prakashlab/octopi-driver-board/Parts/Connectors/FunctionMAX FX20/FX20-120S-0.5SV Specs.pdf

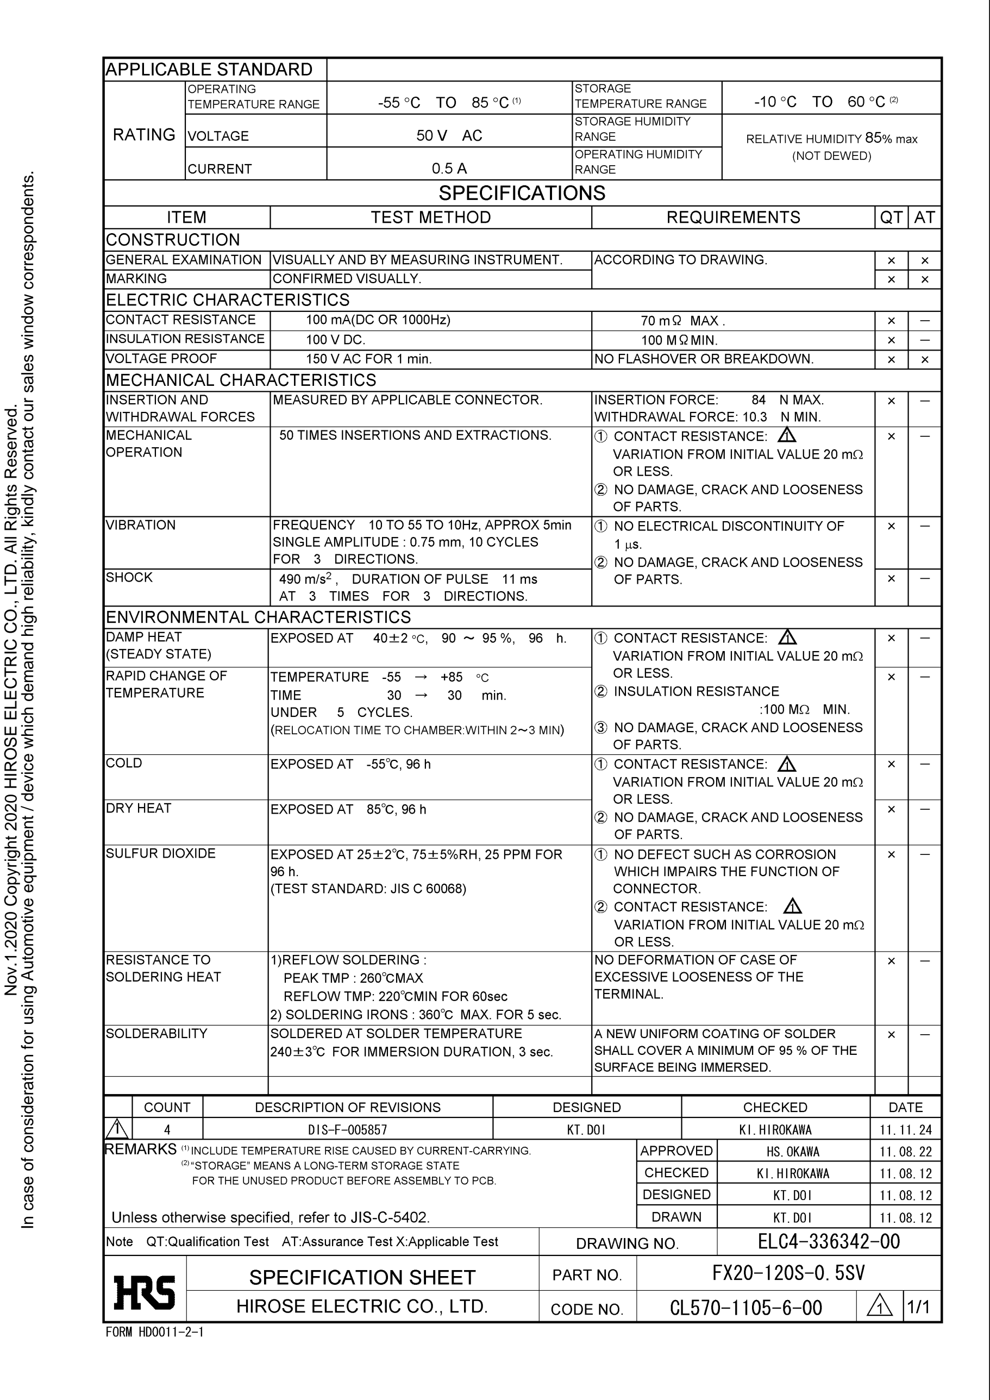
[picture p6: page 1]
