prakashlab/octopi-driver-board/ODSv1.0.0-BP-Jmp/Mechanical Renders/Below Front.png

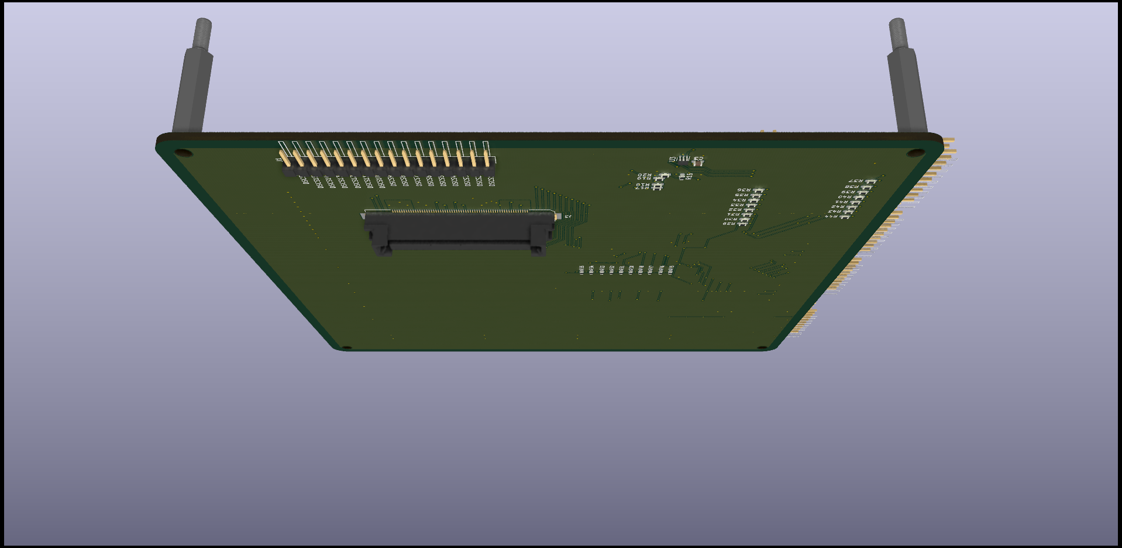
ODSv1.0.0-BP-Jmp/Mechanical Renders/Below Front.png
