prakashlab/octopi-driver-board/ODSv1.0.0-BP-Jmp/Preview Renders/Bottom.png

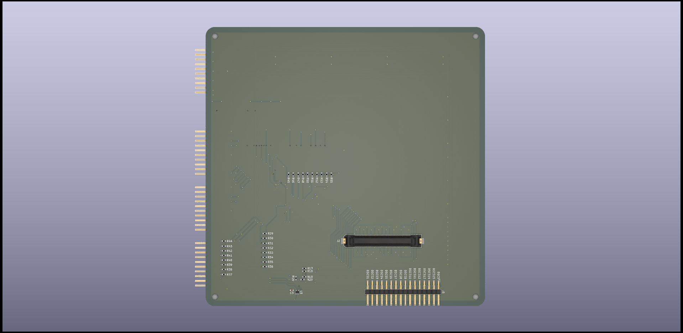
ODSv1.0.0-BP-Jmp/Preview Renders/Bottom.png
