prakashlab/octopi-driver-board/ODSv1.0.0-BP-Jmp/Preview Renders/Top.png

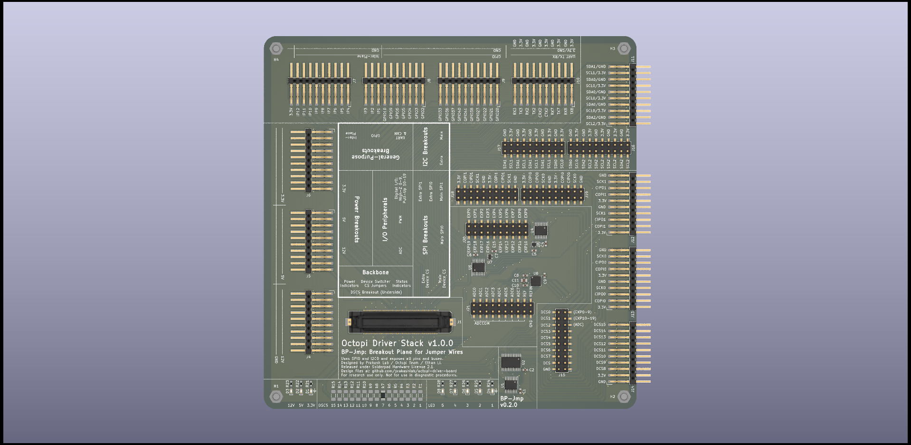
ODSv1.0.0-BP-Jmp/Preview Renders/Top.png
