prakashlab/octopi-driver-board/ODSv1.0.0-BT/Preview Renders/Bottom.png

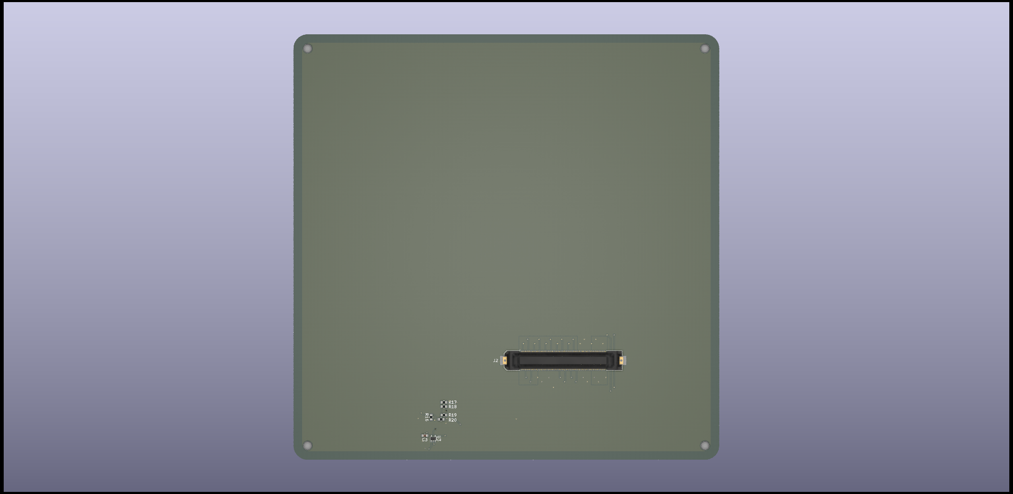
ODSv1.0.0-BT/Preview Renders/Bottom.png
