prakashlab/octopi-driver-board/ODSv1.0.0/Mechanical Renders/2.png

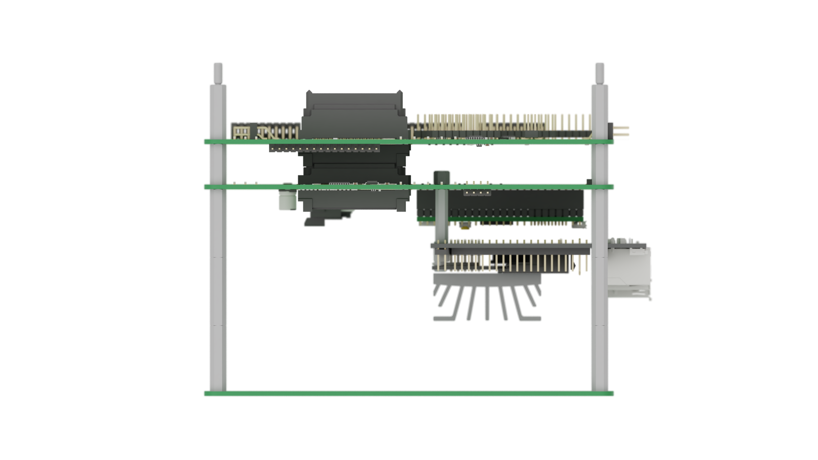
ODSv1.0.0/Mechanical Renders/2.png
