prakashlab/octopi-driver-board/ODSv1.0.0/Mechanical Renders/5.png

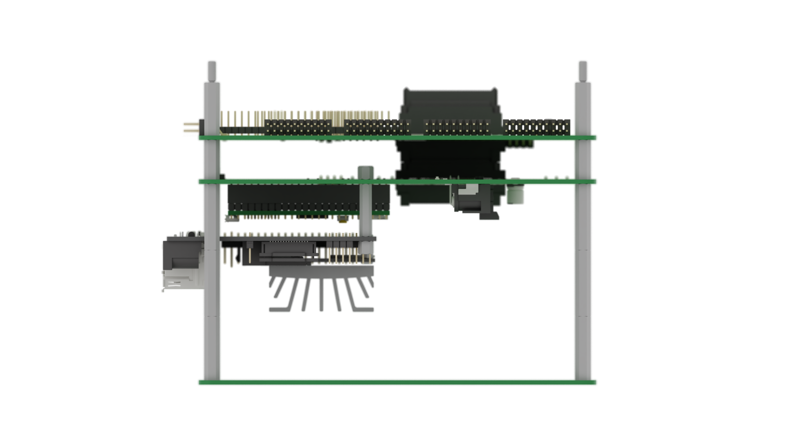
ODSv1.0.0/Mechanical Renders/5.png
