prakashlab/octopi-driver-board/Parts/Connectors/Molex Ultra-Fit/README.md

# Molex Ultra-Fit

Documentation, specifications, 3-D models, and footprints for Molex Ultra-Fit connectors

## License

The PDF and STP files in this directory are copyright Molex. The KICAD_MOD file in this directory was published by Ultra Librarian and is copyright EMA, with the following terms and conditions: "You may incorporate the CONTENT that you are authorized to access into your products or designs which may be distributed without restriction, including for commercial, educational, and open-source purposes. You may not use CONTENT for publishing or creating a library or libraries for sale or distribution for commercial purposes or enabling third parties to do the same."

Ethan Li created the FCStd, STEP, and WRL files in this directory using the STP files in this directory. Those files are copyright Prakash Lab and the Octopi project contributors, and those files are licensed under the [Solderpad Hardware License v2.1](/LICENSE) (the “License”); you may not use files except in compliance with the License, or, at your option, the [Apache License version 2.0](/LICENSE.Apache). You may obtain a copy of the License at https://solderpad.org/licenses/SHL-2.1/

Unless required by applicable law or agreed to in writing, any work distributed under the License is distributed on an “AS IS” BASIS, WITHOUT WARRANTIES OR CONDITIONS OF ANY KIND, either express or implied. See the License for the specific language governing permissions and limitations under the License.
