prakashlab/octopi-driver-board/Parts/Connectors/Samtec SSW/README.md

# Samtec SSW

Documentation and specifications for Samtec SSW connectors

## License

The PDF files in this directory are copyright Samtec.
