prakashlab/octopi-driver-board/Parts/ICs/SPI Peripherals/AD768x/README.md

# Analog Devices 7682/7689

Documentation and specifications for Analog Devices 7682/7689 analog-to-digital converters

## License

The PDF files in this directory are copyright Analog Devices.
