prakashlab/octopi-driver-board/Parts/Passives/Ceramic Capacitors/AVX X7R/README.md

# AVX X7R

Documentation and specifications for AVX X7R capacitors

## License

The PDF files in this directory are copyright AVX.
