prakashlab/octopi-driver-board/Parts/Passives/Electrolytic Capacitors/Nichicon UWT/README.md

# Nichicon UWT

Documentation and specifications for Nichicon UWT capacitors

## License

The PDF files in this directory are copyright Nichicon.
