prakashlab/octopi-driver-board/Parts/Passives/Resistors/Vishay CRCW-HP e3/README.md

# Vishay CRCW-HP e3

Documentation and specifications for Vishay CRCW-HP e3 resistors

## License

The PDF files in this directory are copyright Vishay.
