prakashlab/octopi-driver-board/Parts/Passives/Resistors/Yageo RC L/README.md

# Yageo RC L

Documentation and specifications for Yageo RC L resistors

## License

The PDF files in this directory are copyright Yageo.
