prakashlab/octopi-driver-board/Parts/Connectors/Molex Pico-Lock 1.5mm/504050-0691 Drawing.pdf

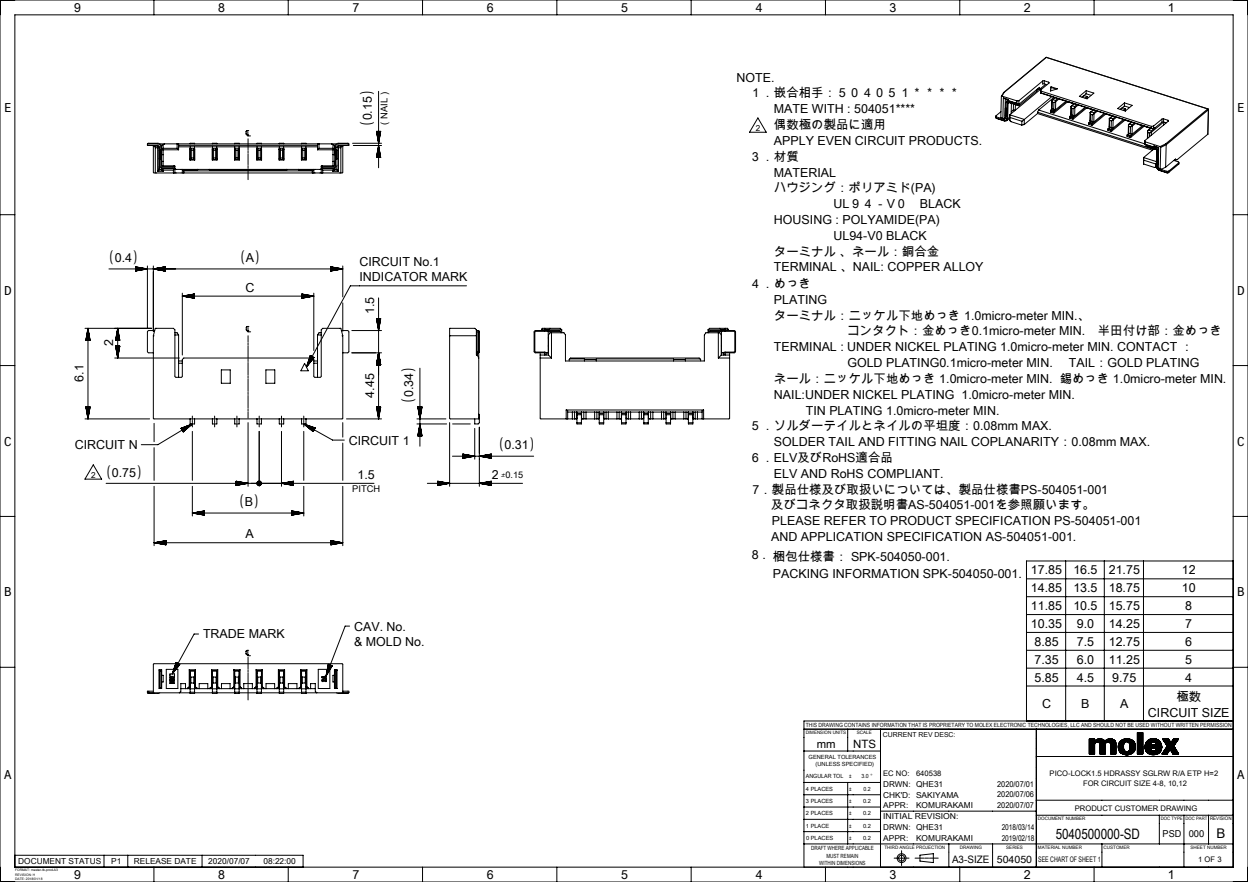
[picture p21: page 1]
DRWN: QHE31; CHK'D: SAKIYAMA; APPR: KOMURAKAMI; INITIAL REVISION:; THIRD ANGLE PROJECTION; DRAWING; SERIES; A3-SIZE 504050; DOCUMENT NUMBER; DOC TYPE DOC PART REVISION; MATERIAL NUMBER; CUSTOMER; SHEET NUMBER; SEE CHART OF SHEET 1; DIMENSION UNITS; SCALE; ANGULAR TOL ±; 4 PLACES; 3 PLACES; 2 PLACES; 1 PLACE; 0 PLACES; UL９４－V０ BLACK; UL94-V0 BLACK; 極数 CIRCUIT SIZE; （NAIL）; TRADE MARK; CIRCUIT 1; CAV. No. & MOLD No.; PITCH; CIRCUIT N; CIRCUIT No.1 INDICATOR MARK

NOTE.
１．嵌合相手：５０４０５１＊＊＊＊
MATE WITH : 504051****
偶数極の製品に適用
APPLY EVEN CIRCUIT PRODUCTS.
MATERIAL
ハウジング：ポリアミド(PA)
HOUSING : POLYAMIDE(PA)
ターミナル 、ネール：銅合金
TERMINAL 、NAIL: COPPER ALLOY
４．めっき
PLATING
ターミナル：ニッケル下地めっき 1.0micro-meter MIN.、
TERMINAL : UNDER NICKEL PLATING 1.0micro-meter MIN. CONTACT ：
ネール：ニッケル下地めっき 1.0micro-meter MIN. 錫めっき 1.0micro-meter MIN.
NAIL:UNDER NICKEL PLATING 1.0micro-meter MIN.
５．ソルダーテイルとネイルの平坦度：0.08mm MAX.
SOLDER TAIL AND FITTING NAIL COPLANARITY：0.08mm MAX.
６．ELV及びRoHS適合品
ELV AND RoHS COMPLIANT.
7．製品仕様及び取扱いについては、製品仕様書PS-504051-001
及びコネクタ取扱説明書AS-504051-001を参照願います。
PLEASE REFER TO PRODUCT SPECIFICATION PS-504051-001
AND APPLICATION SPECIFICATION AS-504051-001.
梱包仕様書： SPK-504050-001.
PACKING INFORMATION SPK-504050-001.

コンタクト：金めっき0.1micro-meter MIN.　半田付け部：金めっき
GOLD PLATING0.1micro-meter MIN.　 TAIL：GOLD PLATING

TIN PLATING 1.0micro-meter MIN.

THIS DRAWING CONTAINS INFORMATION THAT IS PROPRIETARY TO MOLEX ELECTRONIC TECHNOLOGIES, LLC AND SHOULD NOT BE USED WITHOUT WRITTEN PERMISSION
mm NTS

CURRENT REV DESC:

GENERAL TOLERANCES
(UNLESS SPECIFIED)
DRAFT WHERE APPLICABLE
MUST REMAIN
WITHIN DIMENSIONS

PICO-LOCK1.5 HDRASSY SGLRW R/A ETP H=2

FOR CIRCUIT SIZE 4-8, 10,12

PRODUCT CUSTOMER DRAWING
5040500000-SD PSD 000 B

DOCUMENT STATUS P1 RELEASE DATE 2020/07/07 08:22:00

FORMAT: master-tb-prod-A3
REVISION: H
DATE: 2018/01/18

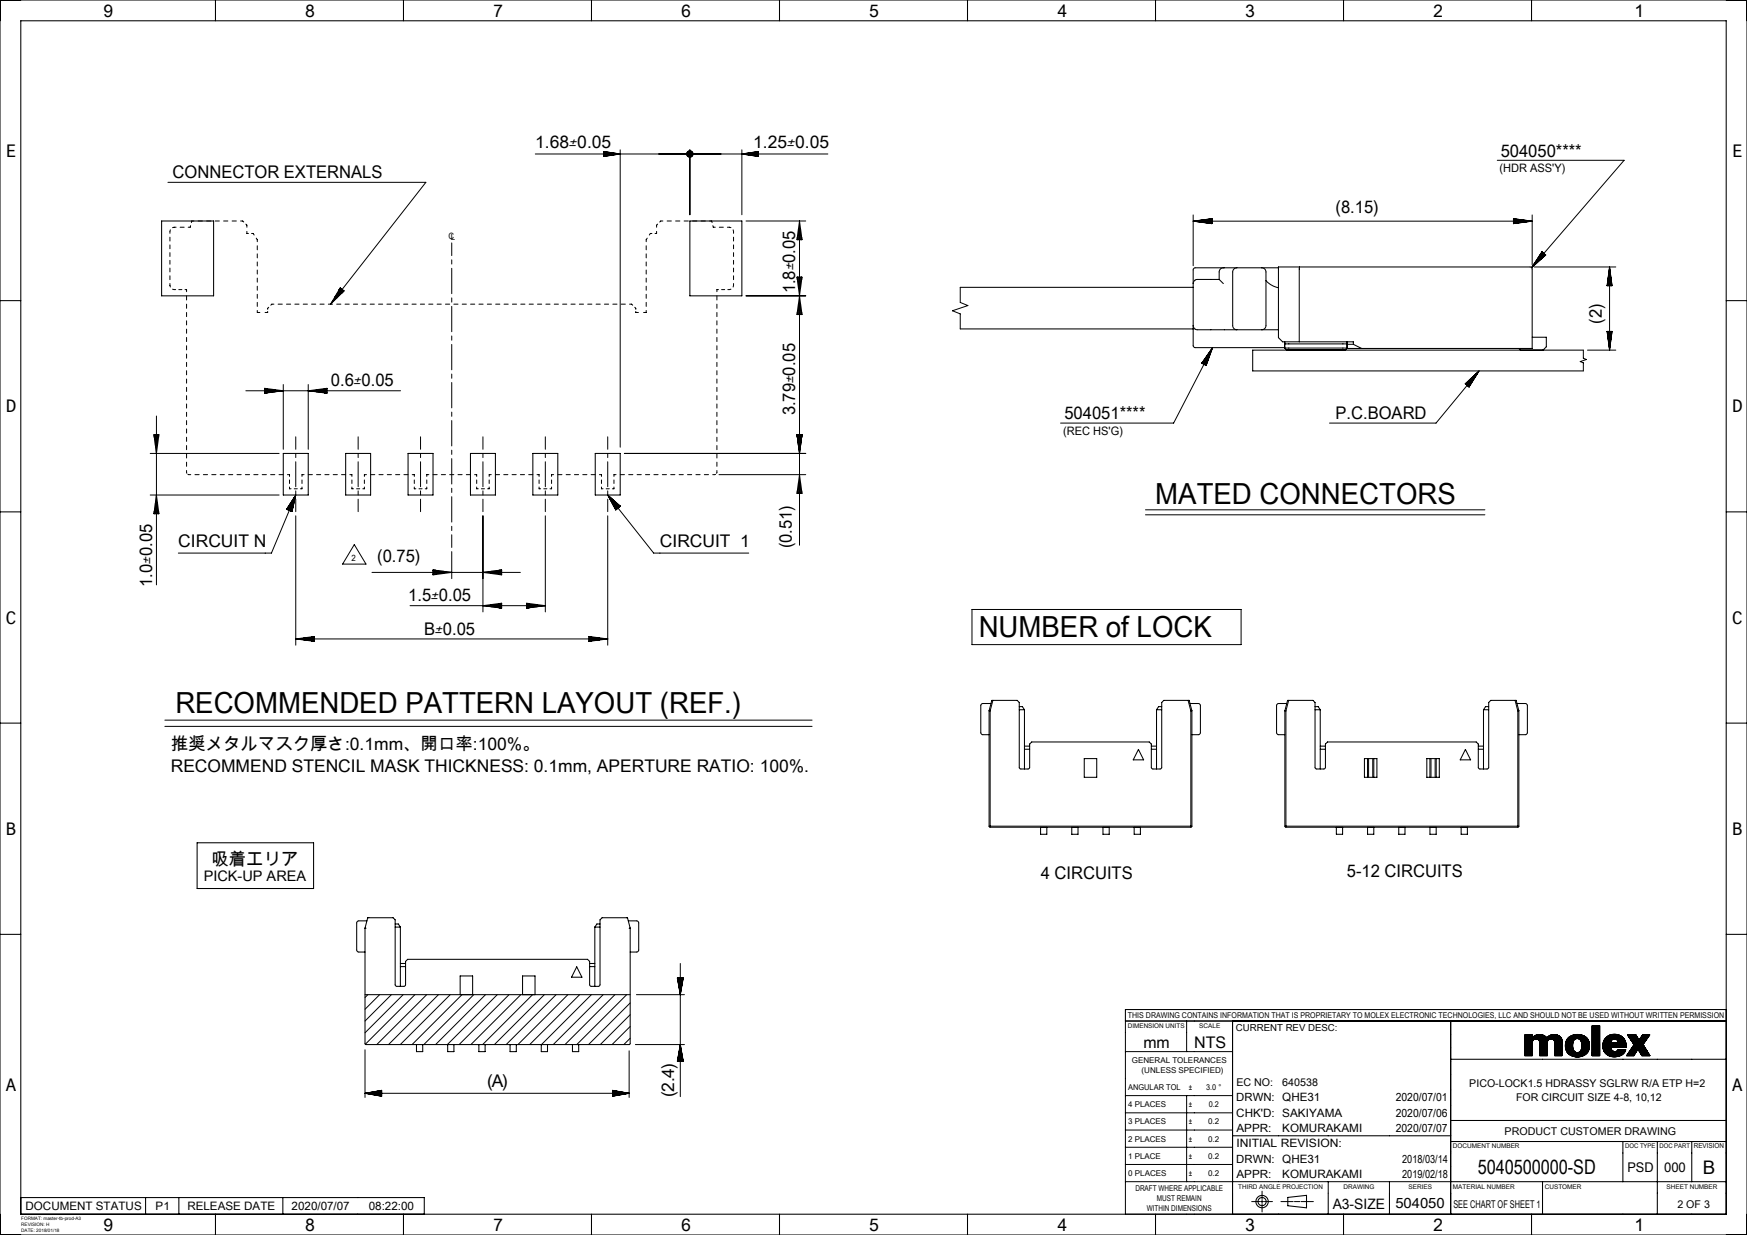
[picture p22: page 2]
SEE CHART OF SHEET 1; DRWN: QHE31; CHK'D: SAKIYAMA; APPR: KOMURAKAMI; DIMENSION UNITS; SCALE; GENERAL TOLERANCES (UNLESS SPECIFIED); ANGULAR TOL ±; 4 PLACES; 3 PLACES; 5-12 CIRCUITS; MATED CONNECTORS; CONNECTOR EXTERNALS; (REC HS'G); (HDR ASS'Y); 4 CIRCUITS; P.C.BOARD; CIRCUIT N; CIRCUIT 1

NUMBER of LOCK

RECOMMENDED PATTERN LAYOUT (REF.)

推奨メタルマスク厚さ:0.1mm、開口率:100%。
RECOMMEND STENCIL MASK THICKNESS: 0.1mm, APERTURE RATIO: 100%. 2.4 ( )

吸着エリア
PICK-UP AREA

THIS DRAWING CONTAINS INFORMATION THAT IS PROPRIETARY TO MOLEX ELECTRONIC TECHNOLOGIES, LLC AND SHOULD NOT BE USED WITHOUT WRITTEN PERMISSION
mm NTS

CURRENT REV DESC:

PICO-LOCK1.5 HDRASSY SGLRW R/A ETP H=2

FOR CIRCUIT SIZE 4-8, 10,12

PRODUCT CUSTOMER DRAWING

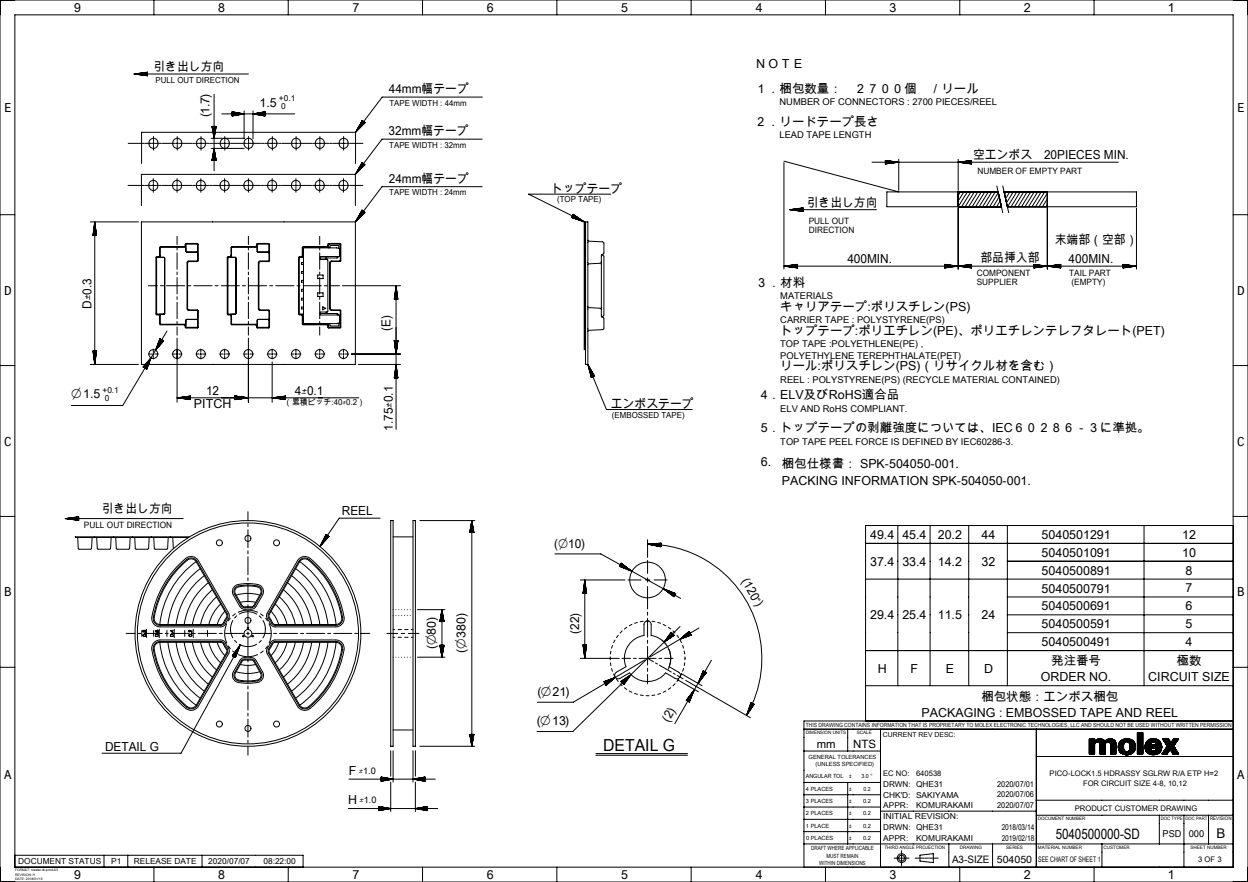
[picture p23: page 3]
DRWN: QHE31; CHK'D: SAKIYAMA; APPR: KOMURAKAMI; DIMENSION UNITS; SCALE; GENERAL TOLERANCES (UNLESS SPECIFIED); ANGULAR TOL ±; 4 PLACES; 3 PLACES; SEE CHART OF SHEET 1; 末端部（空部）; TAPE WIDTH : 24mm; PULL OUT DIRECTION; （累積ピッチ:40±0.2）; COMPONENT SUPPLIER; 24mm幅テープ; REEL; 400MIN.; 発注番号 ORDER NO.; 極数 CIRCUIT SIZE; 梱包状態：エンボス梱包; (TOP TAPE); 引き出し方向; TAPE WIDTH : 32mm; DETAIL G; ２．リードテープ長さ 32mm幅テープ; LEAD TAPE LENGTH; トップテープ; TAIL PART (EMPTY); エンボステープ (EMBOSSED TAPE); 部品挿入部; TAPE WIDTH : 44mm; 44mm幅テープ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

引き出し方向
PULL OUT DIRECTION

ＮＯＴＥ
１．梱包数量：　２７００個　／リール
NUMBER OF CONNECTORS : 2700 PIECES/REEL

空エンボス　20PIECES MIN.
NUMBER OF EMPTY PART

MATERIALS
キャリアテープ:ポリスチレン(PS)
CARRIER TAPE : POLYSTYRENE(PS)
トップテープ:ポリエチレン(PE)、ポリエチレンテレフタレート(PET)
TOP TAPE :POLYETHLENE(PE) ,
POLYETHYLENE TEREPHTHALATE(PET)
リール:ポリスチレン(PS)（リサイクル材を含む）
REEL : POLYSTYRENE(PS) (RECYCLE MATERIAL CONTAINED)
4．ELV及びRoHS適合品
ELV AND RoHS COMPLIANT.
5．トップテープの剥離強度については、IEC６０２８６－３に準拠。
TOP TAPE PEEL FORCE IS DEFINED BY IEC60286-3.
梱包仕様書： SPK-504050-001.
PACKING INFORMATION SPK-504050-001.

PACKAGING : EMBOSSED TAPE AND REEL

THIS DRAWING CONTAINS INFORMATION THAT IS PROPRIETARY TO MOLEX ELECTRONIC TECHNOLOGIES, LLC AND SHOULD NOT BE USED WITHOUT WRITTEN PERMISSION
mm NTS

CURRENT REV DESC:

PICO-LOCK1.5 HDRASSY SGLRW R/A ETP H=2

FOR CIRCUIT SIZE 4-8, 10,12

PRODUCT CUSTOMER DRAWING

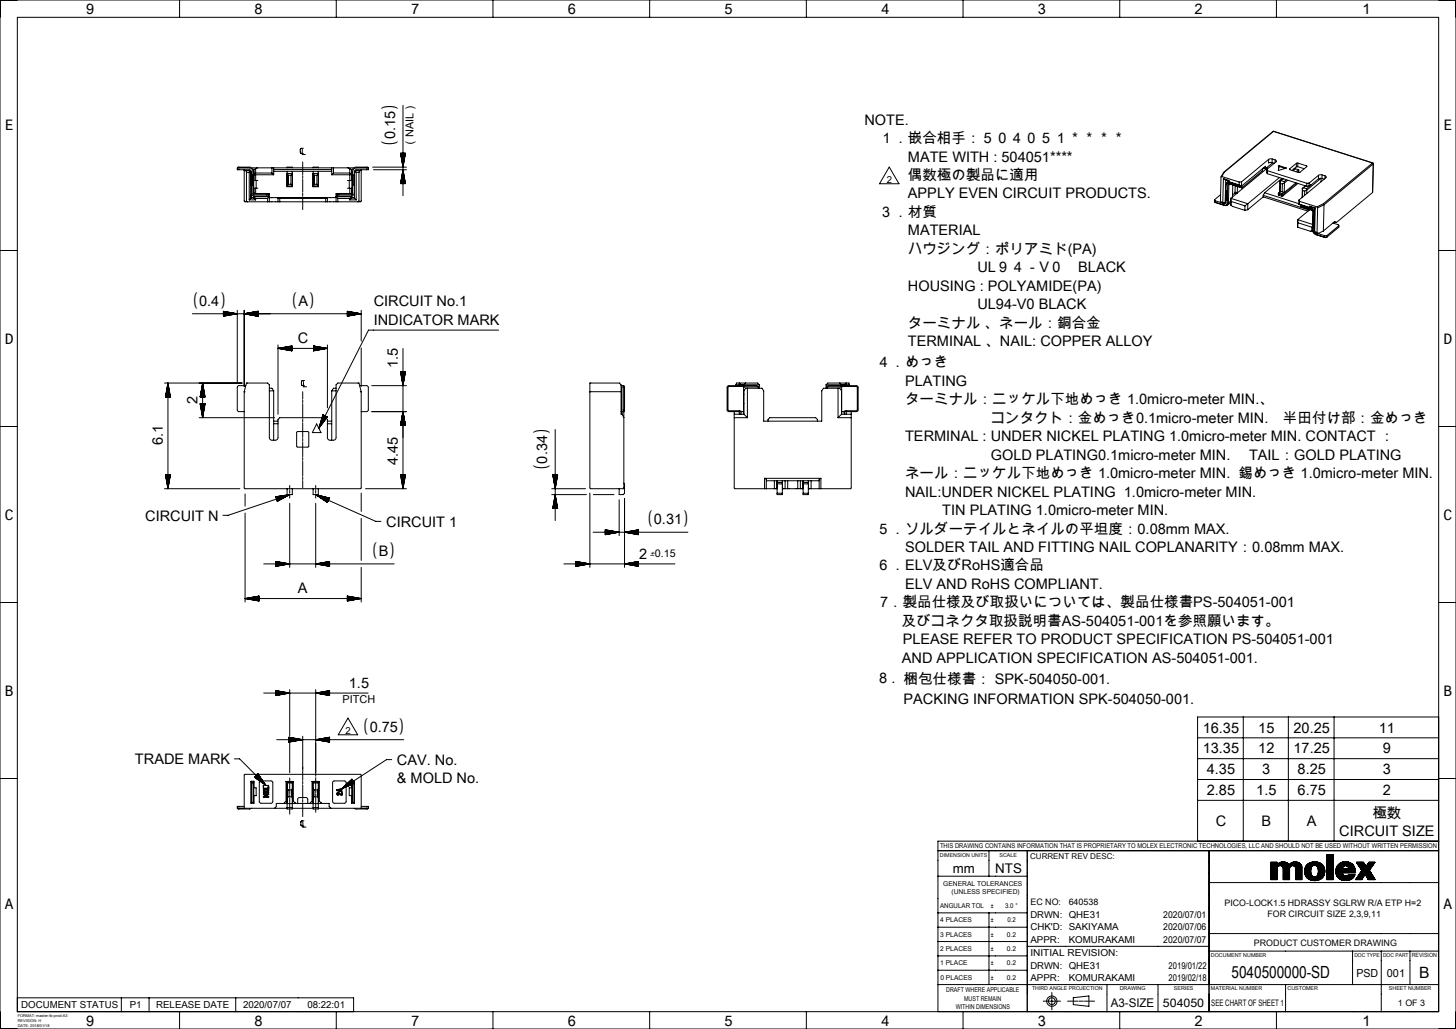
[picture p24: page 4]
DRWN: QHE31; CHK'D: SAKIYAMA; APPR: KOMURAKAMI; SEE CHART OF SHEET 1; DIMENSION UNITS; SCALE; GENERAL TOLERANCES (UNLESS SPECIFIED); ANGULAR TOL ±; 4 PLACES; 3 PLACES; UL９４－V０ BLACK; UL94-V0 BLACK; 極数 CIRCUIT SIZE; （NAIL）; TRADE MARK; CIRCUIT 1; CAV. No. & MOLD No.; CIRCUIT N; CIRCUIT No.1 INDICATOR MARK; PITCH

NOTE.
１．嵌合相手：５０４０５１＊＊＊＊
MATE WITH : 504051****
偶数極の製品に適用
APPLY EVEN CIRCUIT PRODUCTS.
MATERIAL
ハウジング：ポリアミド(PA)
HOUSING : POLYAMIDE(PA)
ターミナル 、ネール：銅合金
TERMINAL 、NAIL: COPPER ALLOY
４．めっき
PLATING
ターミナル：ニッケル下地めっき 1.0micro-meter MIN.、
TERMINAL : UNDER NICKEL PLATING 1.0micro-meter MIN. CONTACT ：
ネール：ニッケル下地めっき 1.0micro-meter MIN. 錫めっき 1.0micro-meter MIN.
NAIL:UNDER NICKEL PLATING 1.0micro-meter MIN.
５．ソルダーテイルとネイルの平坦度：0.08mm MAX.
SOLDER TAIL AND FITTING NAIL COPLANARITY：0.08mm MAX.
６．ELV及びRoHS適合品
ELV AND RoHS COMPLIANT.
7．製品仕様及び取扱いについては、製品仕様書PS-504051-001
及びコネクタ取扱説明書AS-504051-001を参照願います。
PLEASE REFER TO PRODUCT SPECIFICATION PS-504051-001
AND APPLICATION SPECIFICATION AS-504051-001.
梱包仕様書： SPK-504050-001.
PACKING INFORMATION SPK-504050-001.

コンタクト：金めっき0.1micro-meter MIN.　半田付け部：金めっき
GOLD PLATING0.1micro-meter MIN.　 TAIL：GOLD PLATING

TIN PLATING 1.0micro-meter MIN.

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

CURRENT REV DESC:

PICO-LOCK1.5 HDRASSY SGLRW R/A ETP H=2

FOR CIRCUIT SIZE 2,3,9,11

PRODUCT CUSTOMER DRAWING
5040500000-SD PSD 001 B

DOCUMENT STATUS P1 RELEASE DATE 2020/07/07 08:22:01

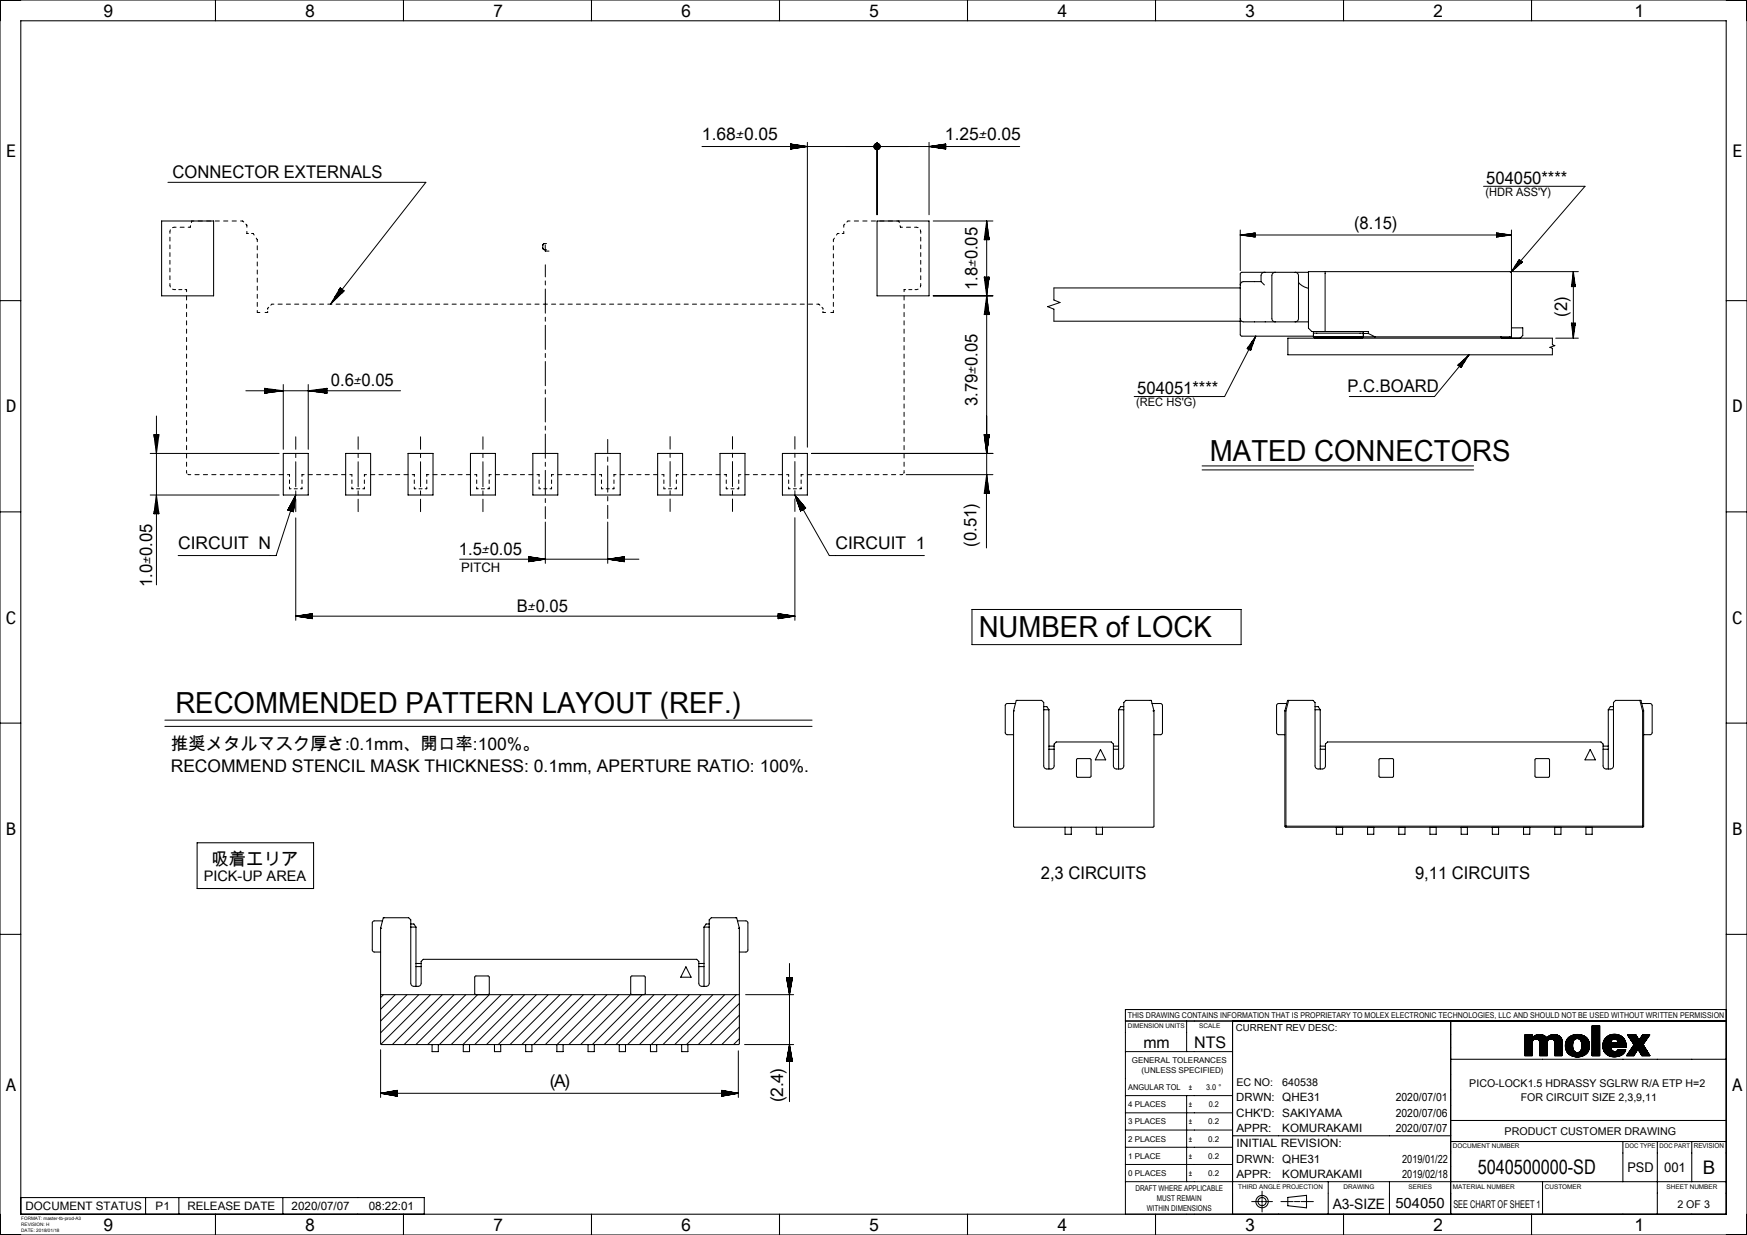
[picture p25: page 5]
SEE CHART OF SHEET 1; DRWN: QHE31; CHK'D: SAKIYAMA; APPR: KOMURAKAMI; DIMENSION UNITS; SCALE; GENERAL TOLERANCES (UNLESS SPECIFIED); ANGULAR TOL ±; 4 PLACES; 3 PLACES; 9,11 CIRCUITS; 504051**** MATED CONNECTORS; CONNECTOR EXTERNALS; (REC HS'G); (HDR ASS'Y); 2,3 CIRCUITS; P.C.BOARD; PITCH; CIRCUIT N; CIRCUIT 1

NUMBER of LOCK

RECOMMENDED PATTERN LAYOUT (REF.)

推奨メタルマスク厚さ:0.1mm、開口率:100%。
RECOMMEND STENCIL MASK THICKNESS: 0.1mm, APERTURE RATIO: 100%.

吸着エリア
PICK-UP AREA

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

CURRENT REV DESC:

PICO-LOCK1.5 HDRASSY SGLRW R/A ETP H=2

FOR CIRCUIT SIZE 2,3,9,11

PRODUCT CUSTOMER DRAWING

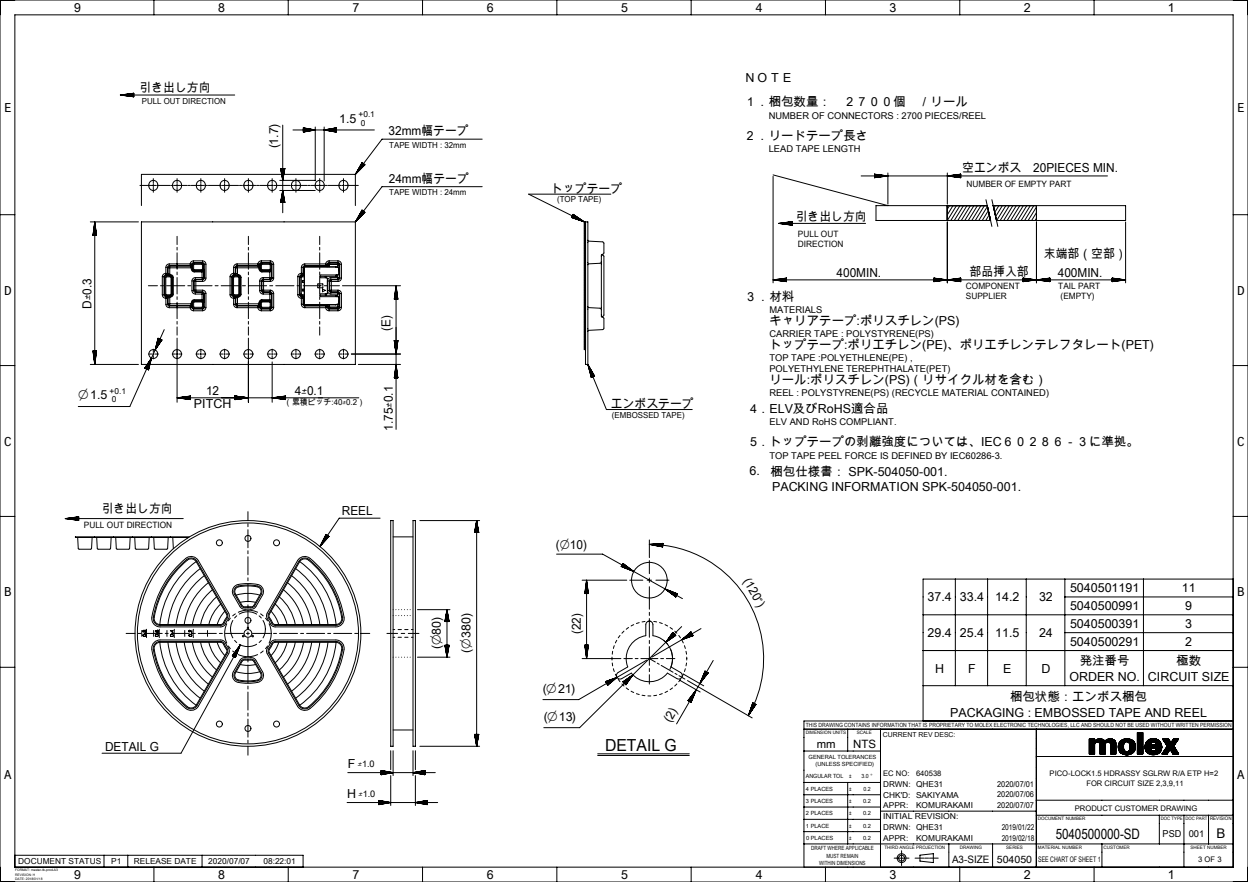
[picture p26: page 6]
DRWN: QHE31; CHK'D: SAKIYAMA; APPR: KOMURAKAMI; DIMENSION UNITS; SCALE; GENERAL TOLERANCES (UNLESS SPECIFIED); ANGULAR TOL ±; 4 PLACES; 3 PLACES; SEE CHART OF SHEET 1; TAIL PART (EMPTY); DETAIL G; 部品挿入部; 400MIN.; 空エンボス 20PIECES MIN.; 32mm幅テープ; (TOP TAPE); 引き出し方向; COMPONENT SUPPLIER; トップテープ; NUMBER OF EMPTY PART; (EMBOSSED TAPE); （累積ピッチ:40±0.2）; エンボステープ; 24mm幅テープ TAPE WIDTH : 24mm; TAPE WIDTH : 32mm; REEL; PULL OUT DIRECTION; 末端部（空部）; 発注番号 ORDER NO.; 極数 CIRCUIT SIZE; 梱包状態：エンボス梱包; PITCH

ＮＯＴＥ
１．梱包数量：　２７００個　／リール
NUMBER OF CONNECTORS : 2700 PIECES/REEL
２．リードテープ長さ
LEAD TAPE LENGTH

引き出し方向
PULL OUT DIRECTION

MATERIALS
キャリアテープ:ポリスチレン(PS)
CARRIER TAPE : POLYSTYRENE(PS)
トップテープ:ポリエチレン(PE)、ポリエチレンテレフタレート(PET)
TOP TAPE :POLYETHLENE(PE) ,
POLYETHYLENE TEREPHTHALATE(PET)
リール:ポリスチレン(PS)（リサイクル材を含む）
REEL : POLYSTYRENE(PS) (RECYCLE MATERIAL CONTAINED)
4．ELV及びRoHS適合品
ELV AND RoHS COMPLIANT.
5．トップテープの剥離強度については、IEC６０２８６－３に準拠。
TOP TAPE PEEL FORCE IS DEFINED BY IEC60286-3.
6. 梱包仕様書： SPK-504050-001.
PACKING INFORMATION SPK-504050-001.

PACKAGING : EMBOSSED TAPE AND REEL

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

CURRENT REV DESC:

PICO-LOCK1.5 HDRASSY SGLRW R/A ETP H=2

FOR CIRCUIT SIZE 2,3,9,11

PRODUCT CUSTOMER DRAWING
