prakashlab/octopi-driver-board/Parts/Connectors/Molex Ultra-Fit/Drawing.pdf

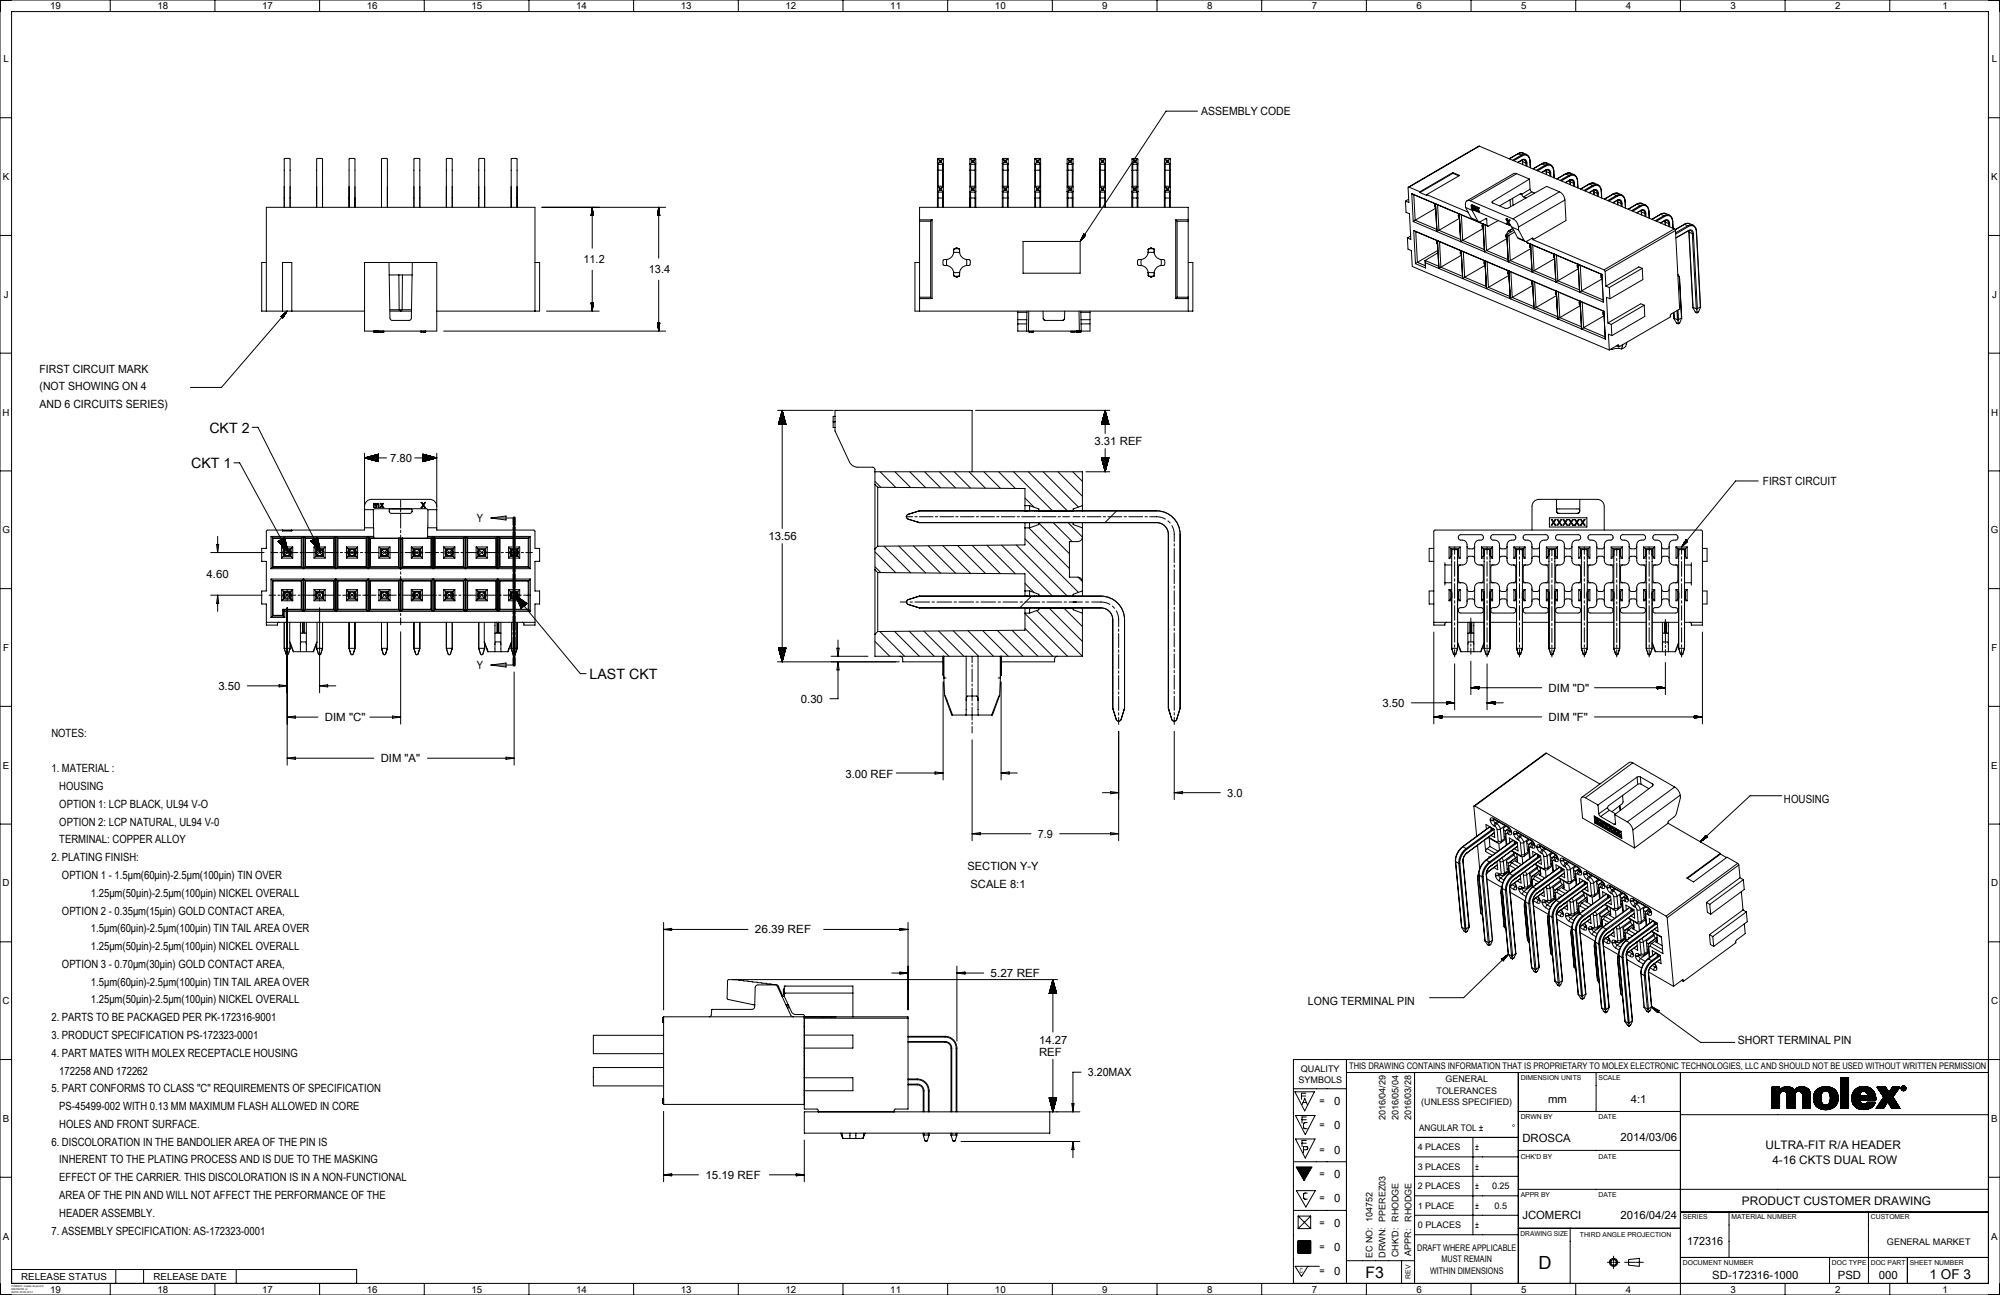
[picture p27: page 1]
GENERAL TOLERANCES (UNLESS SPECIFIED); ANGULAR TOL ±; SERIES; MATERIAL NUMBER; CUSTOMER; GENERAL MARKET; 4 PLACES; 3 PLACES; 2 PLACES; 1 PLACE; 0 PLACES; SHEET NUMBER; DOCUMENT NUMBER; DOC TYPE DOC PART; PSD; DRAWING SIZE; THIRD ANGLE PROJECTION; QUALITY SYMBOLS; DIMENSION UNITS; SCALE; DRWN BY; DATE; DROSCA; CHK'D BY; APPR BY; JCOMERCI; PPEREZ03; RHODGE; DRWN:; CHK'D:; REV; 3.31 REF; REF; 3.20MAX; 5.27 REF; 26.39 REF; 15.19 REF; FIRST CIRCUIT; DIM "F"; DIM "D"; DIM "A"; DIM "C"; 3.00 REF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

FIRST CIRCUIT MARK
(NOT SHOWING ON 4
AND 6 CIRCUITS SERIES)

1. MATERIAL :
HOUSING
OPTION 1: LCP BLACK, UL94 V-O
OPTION 2: LCP NATURAL, UL94 V-0
TERMINAL: COPPER ALLOY
2. PLATING FINISH:
OPTION 1 - 1.5µm(60µin)-2.5µm(100µin) TIN OVER
1.25µm(50µin)-2.5µm(100µin) NICKEL OVERALL
OPTION 2 - 0.35µm(15µin) GOLD CONTACT AREA,
1.5µm(60µin)-2.5µm(100µin) TIN TAIL AREA OVER
OPTION 3 - 0.70µm(30µin) GOLD CONTACT AREA,

LONG TERMINAL PIN

2. PARTS TO BE PACKAGED PER PK-172316-9001
3. PRODUCT SPECIFICATION PS-172323-0001
4. PART MATES WITH MOLEX RECEPTACLE HOUSING
172258 AND 172262
5. PART CONFORMS TO CLASS "C" REQUIREMENTS OF SPECIFICATION
PS-45499-002 WITH 0.13 MM MAXIMUM FLASH ALLOWED IN CORE
HOLES AND FRONT SURFACE.
6. DISCOLORATION IN THE BANDOLIER AREA OF THE PIN IS
INHERENT TO THE PLATING PROCESS AND IS DUE TO THE MASKING
EFFECT OF THE CARRIER. THIS DISCOLORATION IS IN A NON-FUNCTIONAL
AREA OF THE PIN AND WILL NOT AFFECT THE PERFORMANCE OF THE
HEADER ASSEMBLY.

SHORT TERMINAL PIN

THIS DRAWING CONTAINS INFORMATION THAT IS PROPRIETARY TO MOLEX ELECTRONIC TECHNOLOGIES, LLC AND SHOULD NOT BE USED WITHOUT WRITTEN PERMISSION

ULTRA-FIT R/A HEADER
4-16 CKTS DUAL ROW

PRODUCT CUSTOMER DRAWING

7. ASSEMBLY SPECIFICATION: AS-172323-0001

APPR:
DRAFT WHERE APPLICABLE
MUST REMAIN
WITHIN DIMENSIONS

RELEASE STATUS | RELEASE DATE

FORMAT: master-tb-prod-D
REVISION: G
DATE: 2015/12/14

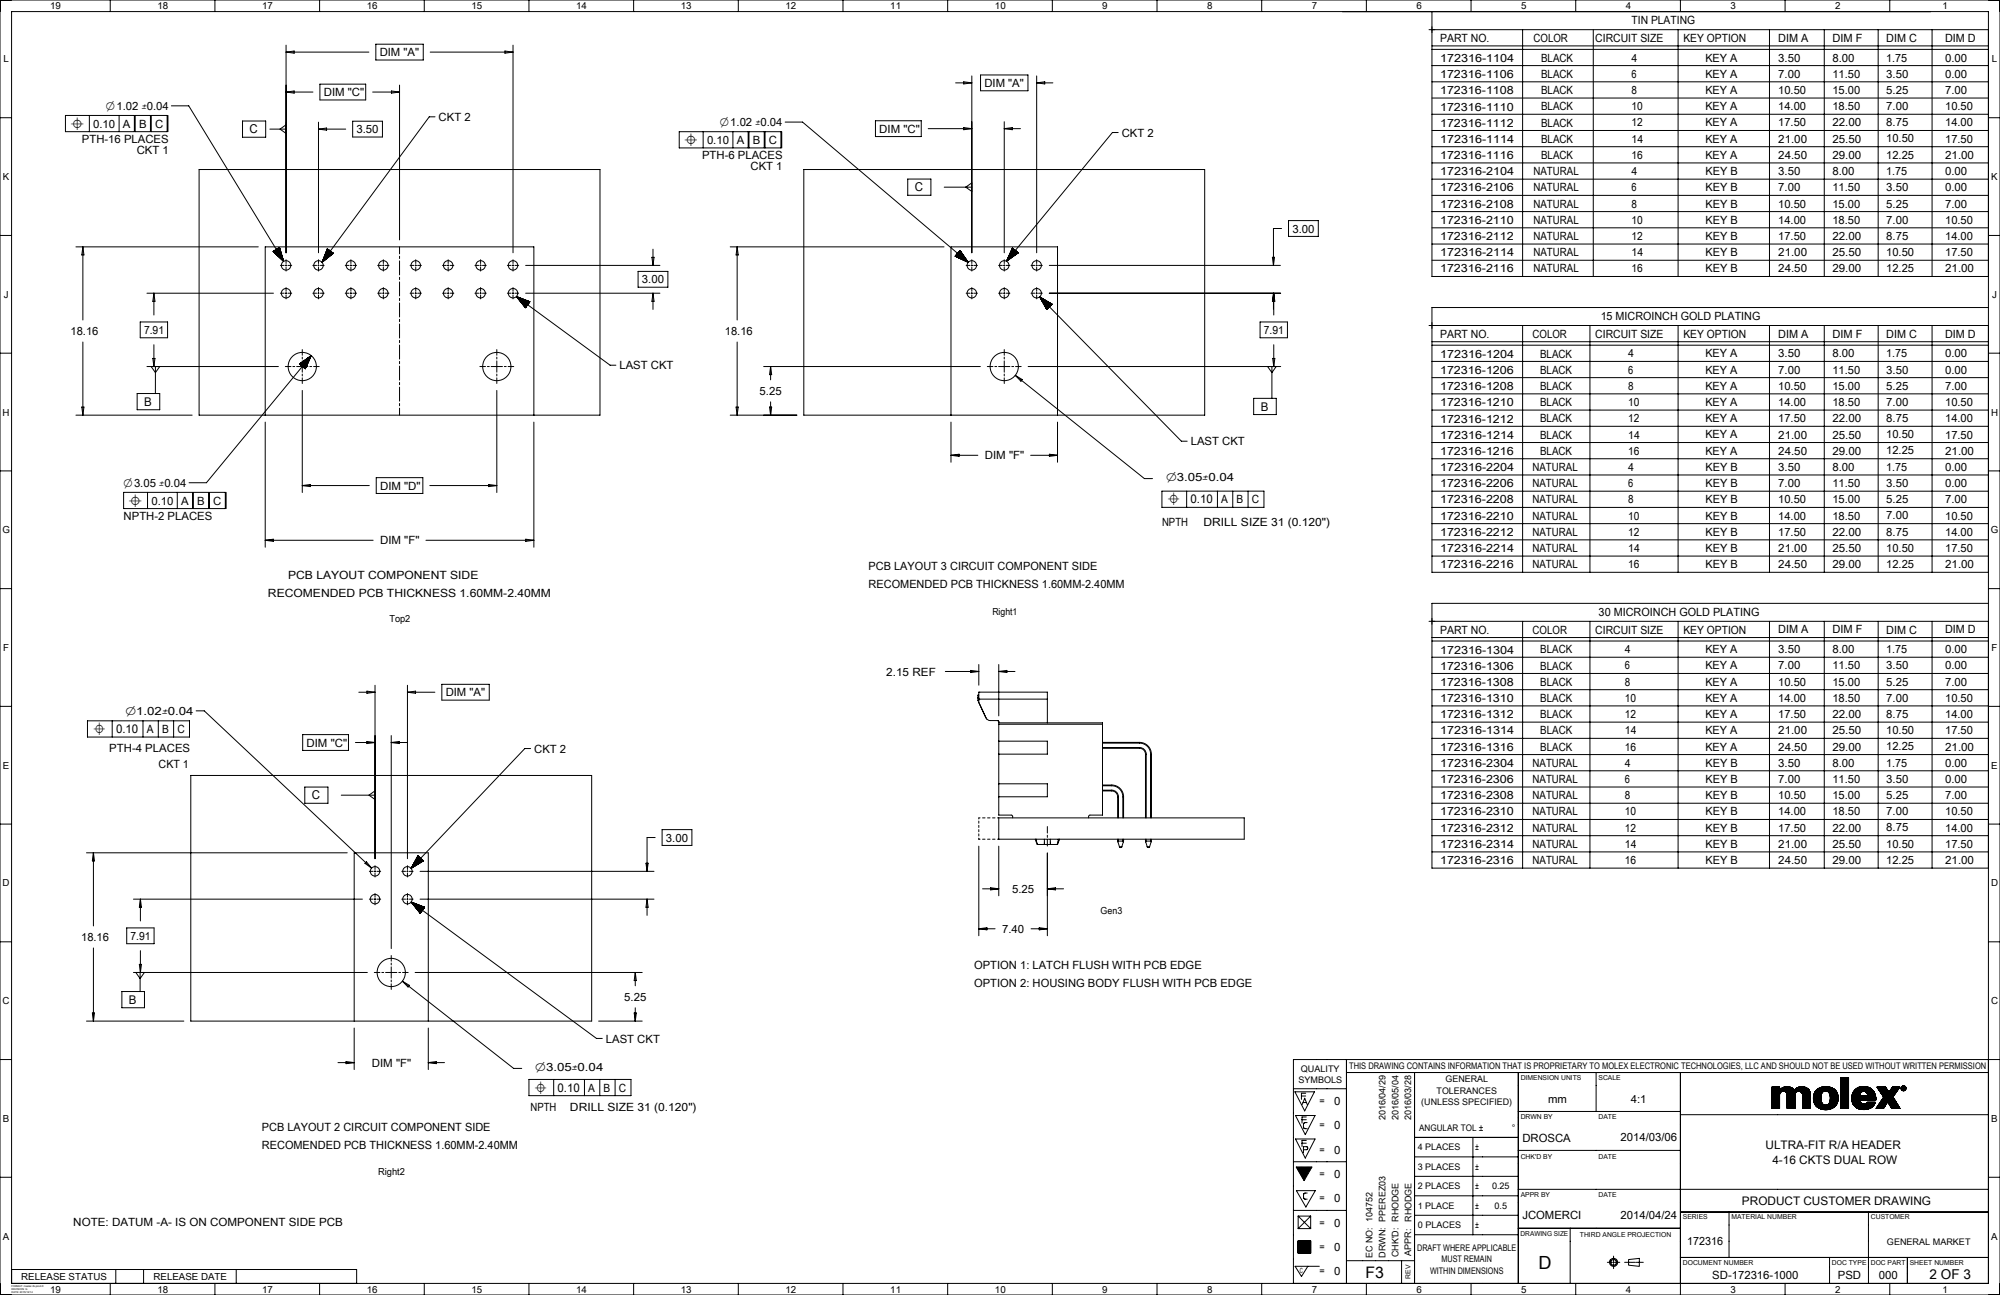
[picture p28: page 2]
GENERAL TOLERANCES (UNLESS SPECIFIED); ANGULAR TOL ±; 4 PLACES; 3 PLACES; QUALITY SYMBOLS; DIMENSION UNITS; SCALE; DRWN BY; DATE; DROSCA; CHK'D BY; JCOMERCI; PPEREZ03; CKT 2; DIM D; BLACK; COLOR; PART NO.; DIM A; DIM F; DIM C; CIRCUIT SIZE; NATURAL; KEY OPTION; TIN PLATING; KEY A; KEY B; Gen3; NPTH; DIM "F"; 2.15 REF; DIM "A"; Right1; DIM "C"; DRILL SIZE 31 (0.120"); DIM "D"; CKT 1; PTH-4 PLACES; Right2; Top2; NPTH-2 PLACES; 30 MICROINCH GOLD PLATING; PTH-16 PLACES CKT 1; LAST CKT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

15 MICROINCH GOLD PLATING
CIRCUIT SIZE

PCB LAYOUT 3 CIRCUIT COMPONENT SIDE
RECOMENDED PCB THICKNESS 1.60MM-2.40MM

PCB LAYOUT COMPONENT SIDE

OPTION 1: LATCH FLUSH WITH PCB EDGE
OPTION 2: HOUSING BODY FLUSH WITH PCB EDGE

THIS DRAWING CONTAINS INFORMATION THAT IS PROPRIETARY TO MOLEX ELECTRONIC TECHNOLOGIES, LLC AND SHOULD NOT BE USED WITHOUT WRITTEN PERMISSION

PCB LAYOUT 2 CIRCUIT COMPONENT SIDE

ULTRA-FIT R/A HEADER
4-16 CKTS DUAL ROW

NOTE: DATUM -A- IS ON COMPONENT SIDE PCB

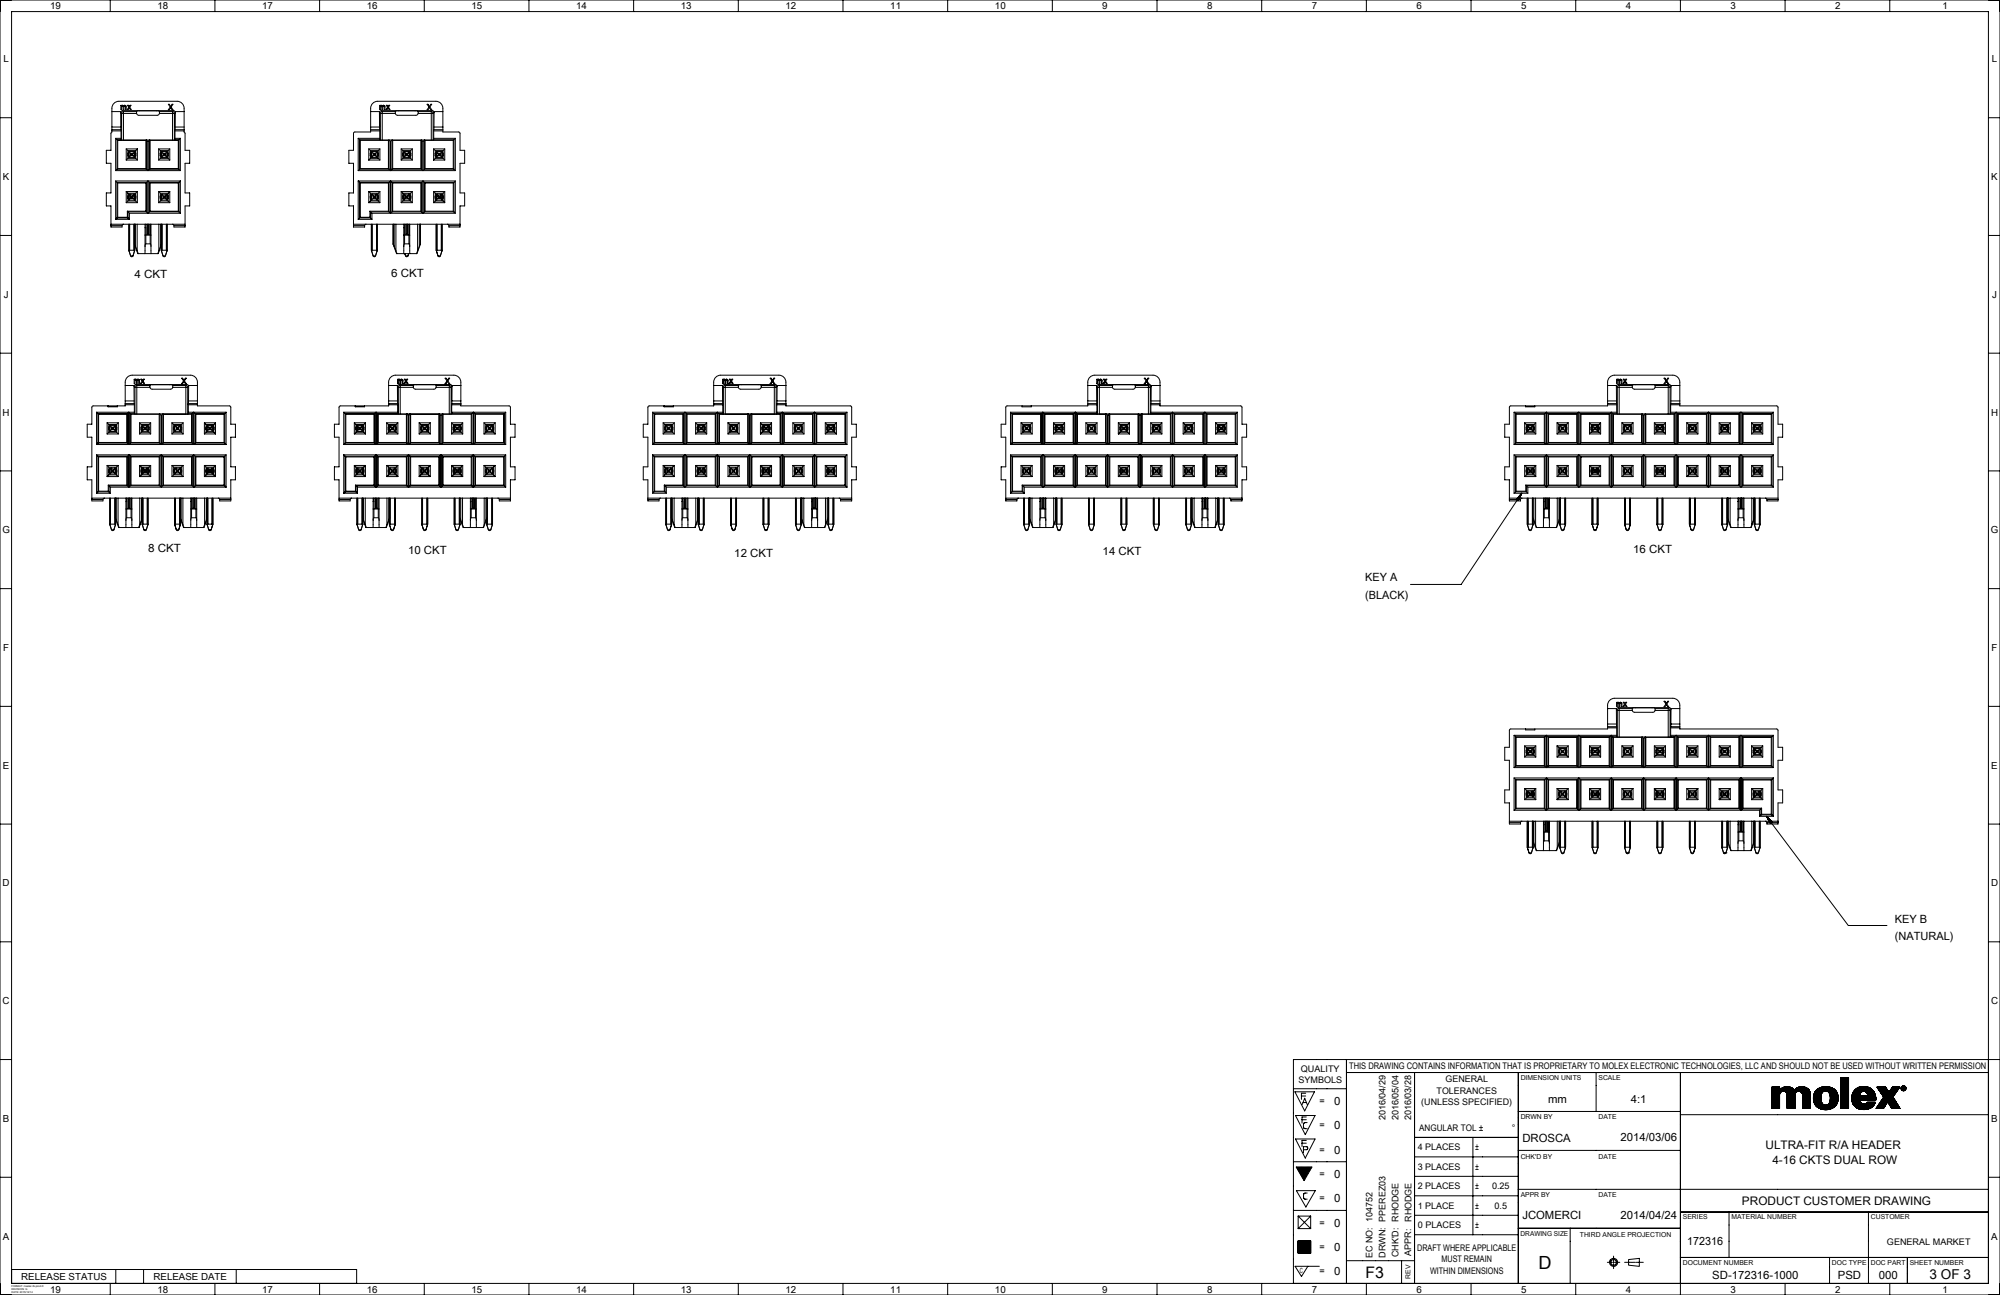
[picture p29: page 3]
GENERAL TOLERANCES (UNLESS SPECIFIED); ANGULAR TOL ±; 4 PLACES; 3 PLACES; QUALITY SYMBOLS; DIMENSION UNITS; SCALE; DRWN BY; DATE; DROSCA; CHK'D BY; JCOMERCI; PPEREZ03; 8 CKT; 6 CKT; 10 CKT; 4 CKT; 12 CKT; 14 CKT; 16 CKT; KEY A; (BLACK); KEY B; (NATURAL)

THIS DRAWING CONTAINS INFORMATION THAT IS PROPRIETARY TO MOLEX ELECTRONIC TECHNOLOGIES, LLC AND SHOULD NOT BE USED WITHOUT WRITTEN PERMISSION

ULTRA-FIT R/A HEADER
4-16 CKTS DUAL ROW
