prakashlab/octopi-driver-board/Parts/Connectors/Samtec SSW/SSW-1xx-22-xx-vs-xx Drawing.pdf

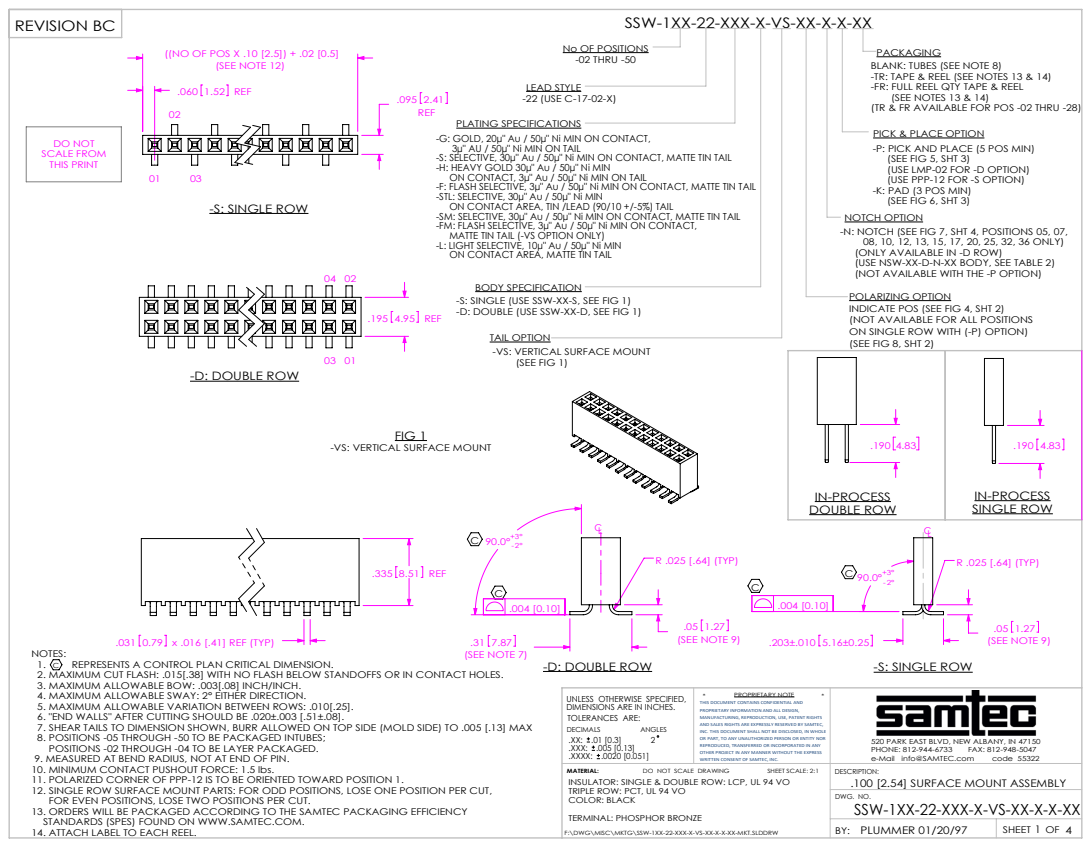
[picture p30: page 1]
DO NOT SCALE FROM THIS PRINT; .031 0.79 x .016 [.41] REF (TYP); .335 8.51 REF; .195 4.95 REF; .31 7.87 (SEE NOTE 7); .05 1.27 (SEE NOTE 9); R .025 [.64] (TYP); -D: DOUBLE ROW; (SEE NOTE 9); (SEE NOTE 12); .060 1.52 REF; -S: SINGLE ROW; LEAD STYLE -22 (USE C-17-02-X); DOUBLE ROW; SINGLE ROW; FIG 1; SHEET OF; PLUMMER 01/20/97; REVISION BC

SSW-1XX-22-XXX-X-VS-XX-X-X-XX

((NO OF POS X .10 [2.5]) + .02 [0.5]

No OF POSITIONS
-02 THRU -50

PACKAGING
BLANK: TUBES (SEE NOTE 8)
-TR: TAPE & REEL (SEE NOTES 13 & 14)
-FR: FULL REEL QTY TAPE & REEL
(SEE NOTES 13 & 14)
(TR & FR AVAILABLE FOR POS -02 THRU -28)

PLATING SPECIFICATIONS
-G: GOLD, 20µ" Au / 50µ" Ni MIN ON CONTACT,
3µ" AU / 50µ" Ni MIN ON TAIL
-S: SELECTIVE, 30µ" Au / 50µ" Ni MIN ON CONTACT, MATTE TIN TAIL
-H: HEAVY GOLD 30µ" Au / 50µ" Ni MIN
ON CONTACT, 3µ" Au / 50µ" Ni MIN ON TAIL
-F: FLASH SELECTIVE, 3µ" Au / 50µ" Ni MIN ON CONTACT, MATTE TIN TAIL
-STL: SELECTIVE, 30µ" Au / 50µ" Ni MIN
ON CONTACT AREA, TIN /LEAD (90/10 +/-5%) TAIL
-SM: SELECTIVE, 30µ" Au / 50µ" Ni MIN ON CONTACT, MATTE TIN TAIL
-FM: FLASH SELECTIVE, 3µ" Au / 50µ" Ni MIN ON CONTACT,
MATTE TIN TAIL (-VS OPTION ONLY)
-L: LIGHT SELECTIVE, 10µ" Au / 50µ" Ni MIN
ON CONTACT AREA, MATTE TIN TAIL

PICK & PLACE OPTION
-P: PICK AND PLACE (5 POS MIN)
(SEE FIG 5, SHT 3)
(USE LMP-02 FOR -D OPTION)
(USE PPP-12 FOR -S OPTION)
-K: PAD (3 POS MIN)
(SEE FIG 6, SHT 3)

NOTCH OPTION
-N: NOTCH (SEE FIG 7, SHT 4, POSITIONS 05, 07,
08, 10, 12, 13, 15, 17, 20, 25, 32, 36 ONLY)
(ONLY AVAILABLE IN -D ROW)
(USE NSW-XX-D-N-XX BODY, SEE TABLE 2)
(NOT AVAILABLE WITH THE -P OPTION)
POLARIZING OPTION
INDICATE POS (SEE FIG 4, SHT 2)
(NOT AVAILABLE FOR ALL POSITIONS
ON SINGLE ROW WITH (-P) OPTION)
(SEE FIG 8, SHT 2)

BODY SPECIFICATION
-S: SINGLE (USE SSW-XX-S, SEE FIG 1)
-D: DOUBLE (USE SSW-XX-D, SEE FIG 1)

TAIL OPTION
-VS: VERTICAL SURFACE MOUNT
(SEE FIG 1)

NOTES:
1. REPRESENTS A CONTROL PLAN CRITICAL DIMENSION.
2. MAXIMUM CUT FLASH: .015[.38] WITH NO FLASH BELOW STANDOFFS OR IN CONTACT HOLES.
3. MAXIMUM ALLOWABLE BOW: .003[.08] INCH/INCH.
4. MAXIMUM ALLOWABLE SWAY: 2° EITHER DIRECTION.
5. MAXIMUM ALLOWABLE VARIATION BETWEEN ROWS: .010[.25].
6. "END WALLS" AFTER CUTTING SHOULD BE .020±.003 [.51±.08].
7. SHEAR TAILS TO DIMENSION SHOWN, BURR ALLOWED ON TOP SIDE (MOLD SIDE) TO .005 [.13] MAX
8. POSITIONS -05 THROUGH -50 TO BE PACKAGED INTUBES;
POSITIONS -02 THROUGH -04 TO BE LAYER PACKAGED.
9. MEASURED AT BEND RADIUS, NOT AT END OF PIN.
10. MINIMUM CONTACT PUSHOUT FORCE: 1.5 lbs.
11. POLARIZED CORNER OF PPP-12 IS TO BE ORIENTED TOWARD POSITION 1.
12. SINGLE ROW SURFACE MOUNT PARTS: FOR ODD POSITIONS, LOSE ONE POSITION PER CUT,
FOR EVEN POSITIONS, LOSE TWO POSITIONS PER CUT.
13. ORDERS WILL BE PACKAGED ACCORDING TO THE SAMTEC PACKAGING EFFICIENCY
STANDARDS (SPES) FOUND ON WWW.SAMTEC.COM.
14. ATTACH LABEL TO EACH REEL.

UNLESS OTHERWISE SPECIFIED, DIMENSIONS ARE IN INCHES. TOLERANCES ARE: DECIMALS ANGLES .XX: .01 [0.3] 2 .XXX: .005 [0.13] .XXXX: .0020 [0.051] | * PROPRIETARY NOTE * THIS DOCUMENT CONTAINS CONFIDENTIAL AND PROPRIETARY INFORMATION AND ALL DESIGN, MANUFACTURING, REPRODUCTION, USE, PATENT RIGHTS AND SALES RIGHTS ARE EXPRESSLY RESERVED BY SAMTEC, INC. THIS DOCUMENT SHALL NOT BE DISCLOSED, IN WHOLE OR PART, TO ANY UNAUTHORIZED PERSON OR ENTITY NOR REPRODUCED, TRANSFERRED OR INCORPORATED IN ANY OTHER PROJECT IN ANY MANNER WITHOUT THE EXPRESS WRITTEN CONSENT OF SAMTEC, INC. | 520 PARK EAST BLVD, NEW ALBANY, IN 47150 PHONE: 812-944-6733 FAX: 812-948-5047 e-Mail info@SAMTEC.com code 55322

MATERIAL: DO NOT SCALE DRAWING SHEET SCALE: 2:1 INSULATOR: SINGLE & DOUBLE ROW: LCP, UL 94 VO TRIPLE ROW: PCT, UL 94 VO COLOR: BLACK TERMINAL: PHOSPHOR BRONZE F:\DWG\MISC\MKTG\SSW-1XX-22-XXX-X-VS-XX-X-X-XX-MKT.SLDDRW | | DESCRIPTION: .100 [2.54] SURFACE MOUNT ASSEMBLY

DWG. NO.

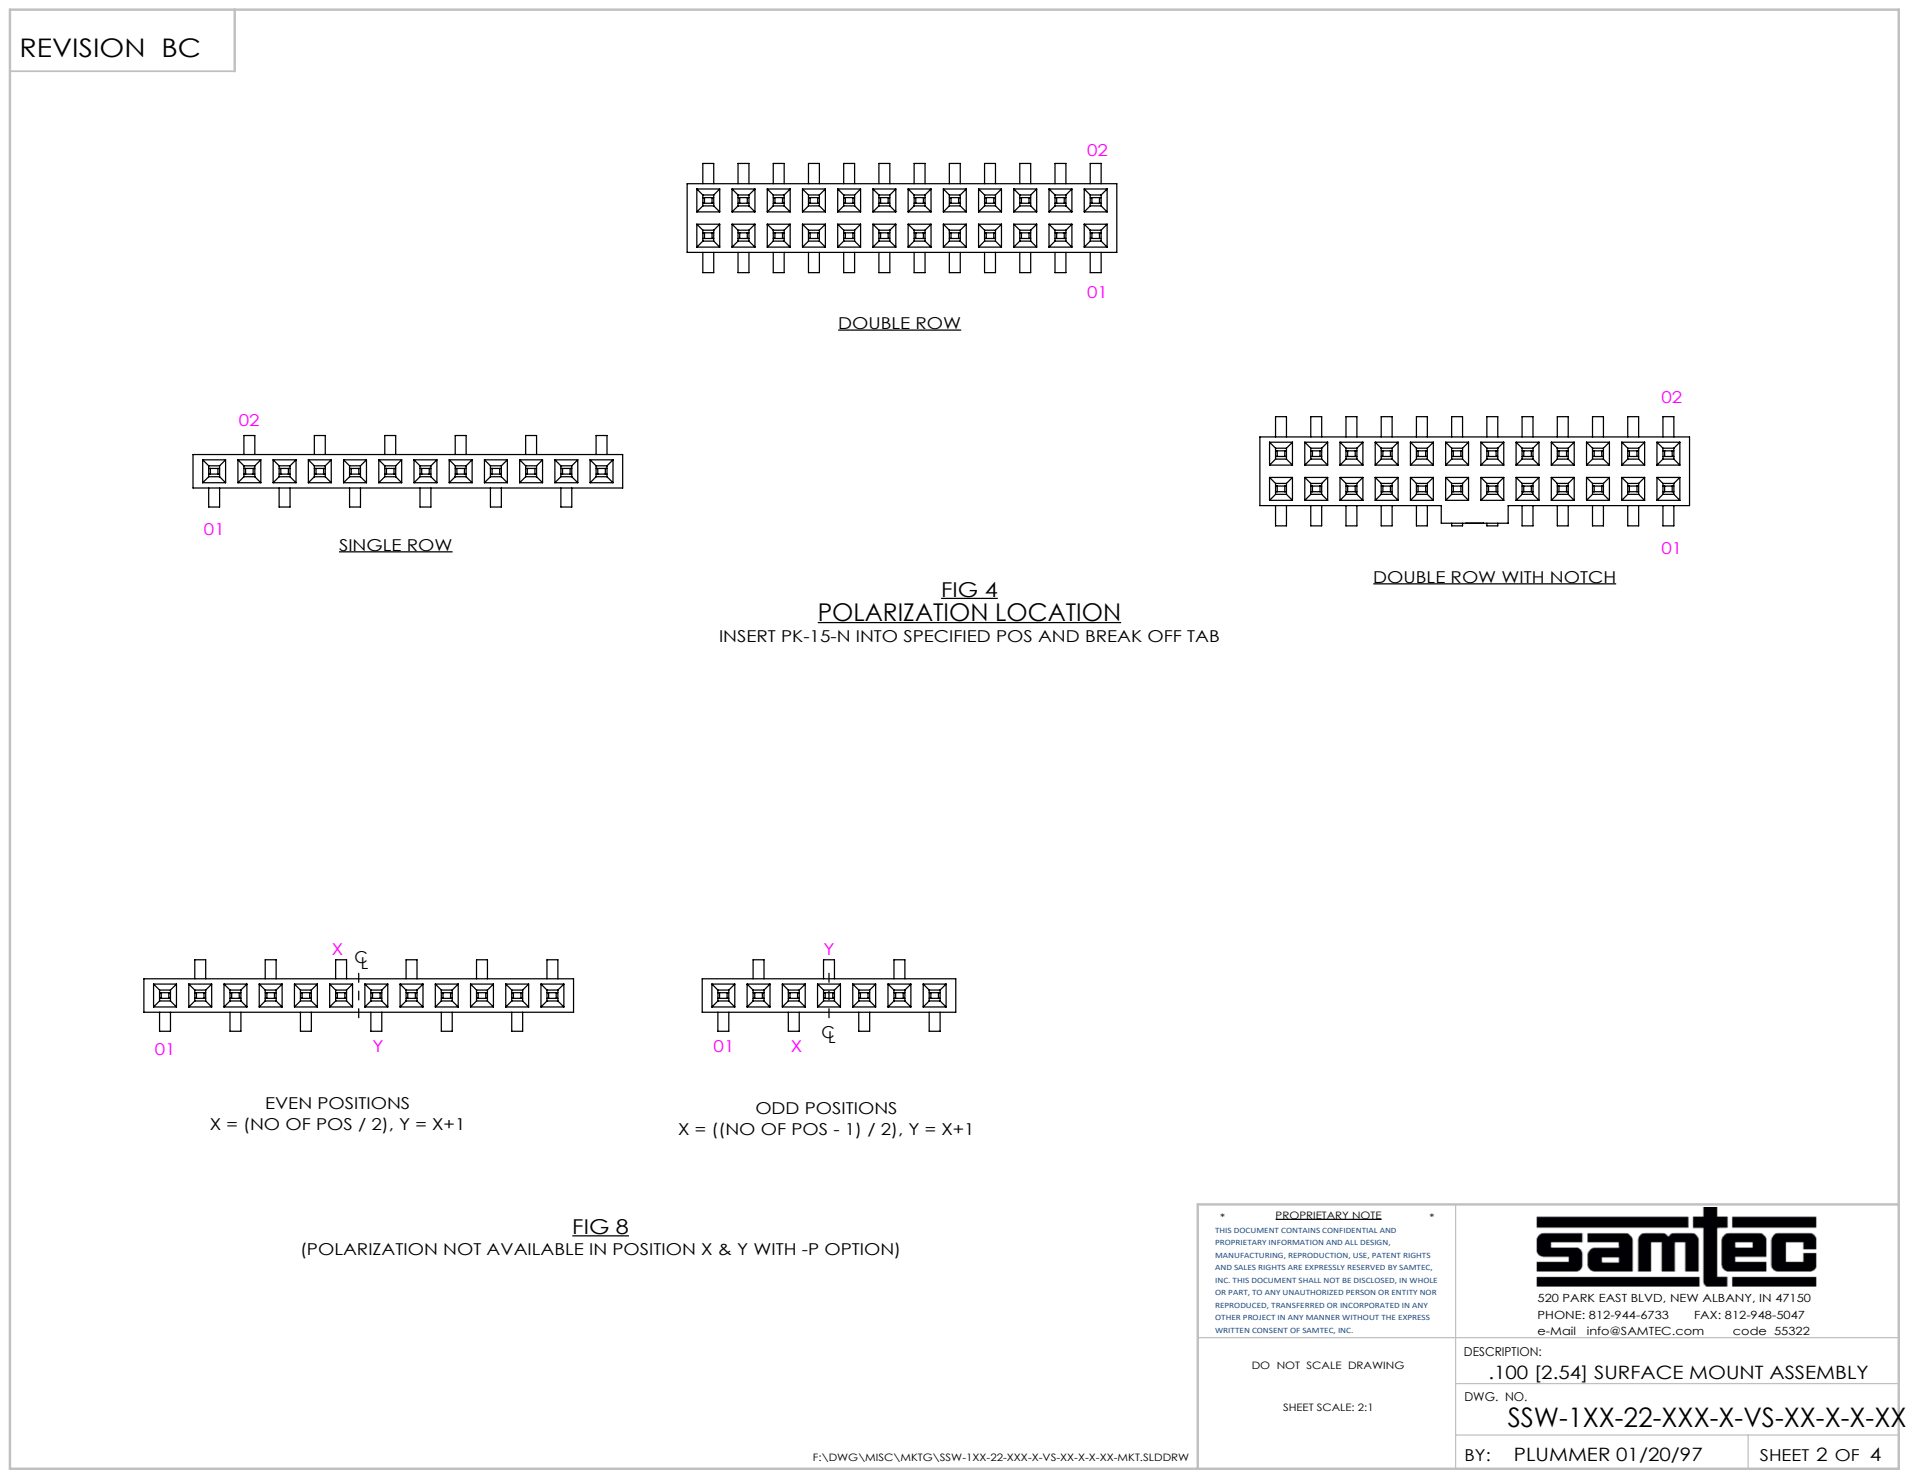
[picture p31: page 2]
SINGLE ROW; DOUBLE ROW; FIG 4 POLARIZATION LOCATION; FIG 8; ODD POSITIONS; SHEET OF; PLUMMER 01/20/97

DOUBLE ROW WITH NOTCH

INSERT PK-15-N INTO SPECIFIED POS AND BREAK OFF TAB

EVEN POSITIONS
X = (NO OF POS / 2), Y = X+1

X = ((NO OF POS - 1) / 2), Y = X+1

* PROPRIETARY NOTE * THIS DOCUMENT CONTAINS CONFIDENTIAL AND PROPRIETARY INFORMATION AND ALL DESIGN, MANUFACTURING, REPRODUCTION, USE, PATENT RIGHTS AND SALES RIGHTS ARE EXPRESSLY RESERVED BY SAMTEC, INC. THIS DOCUMENT SHALL NOT BE DISCLOSED, IN WHOLE OR PART, TO ANY UNAUTHORIZED PERSON OR ENTITY NOR REPRODUCED, TRANSFERRED OR INCORPORATED IN ANY OTHER PROJECT IN ANY MANNER WITHOUT THE EXPRESS WRITTEN CONSENT OF SAMTEC, INC. | 520 PARK EAST BLVD, NEW ALBANY, IN 47150 PHONE: 812-944-6733 FAX: 812-948-5047 e-Mail info@SAMTEC.com code 55322

(POLARIZATION NOT AVAILABLE IN POSITION X & Y WITH -P OPTION)

DO NOT SCALE DRAWING SHEET SCALE: 2:1 | DESCRIPTION:

SSW-1XX-22-XXX-X-VS-XX-X-X-XX DWG. NO.

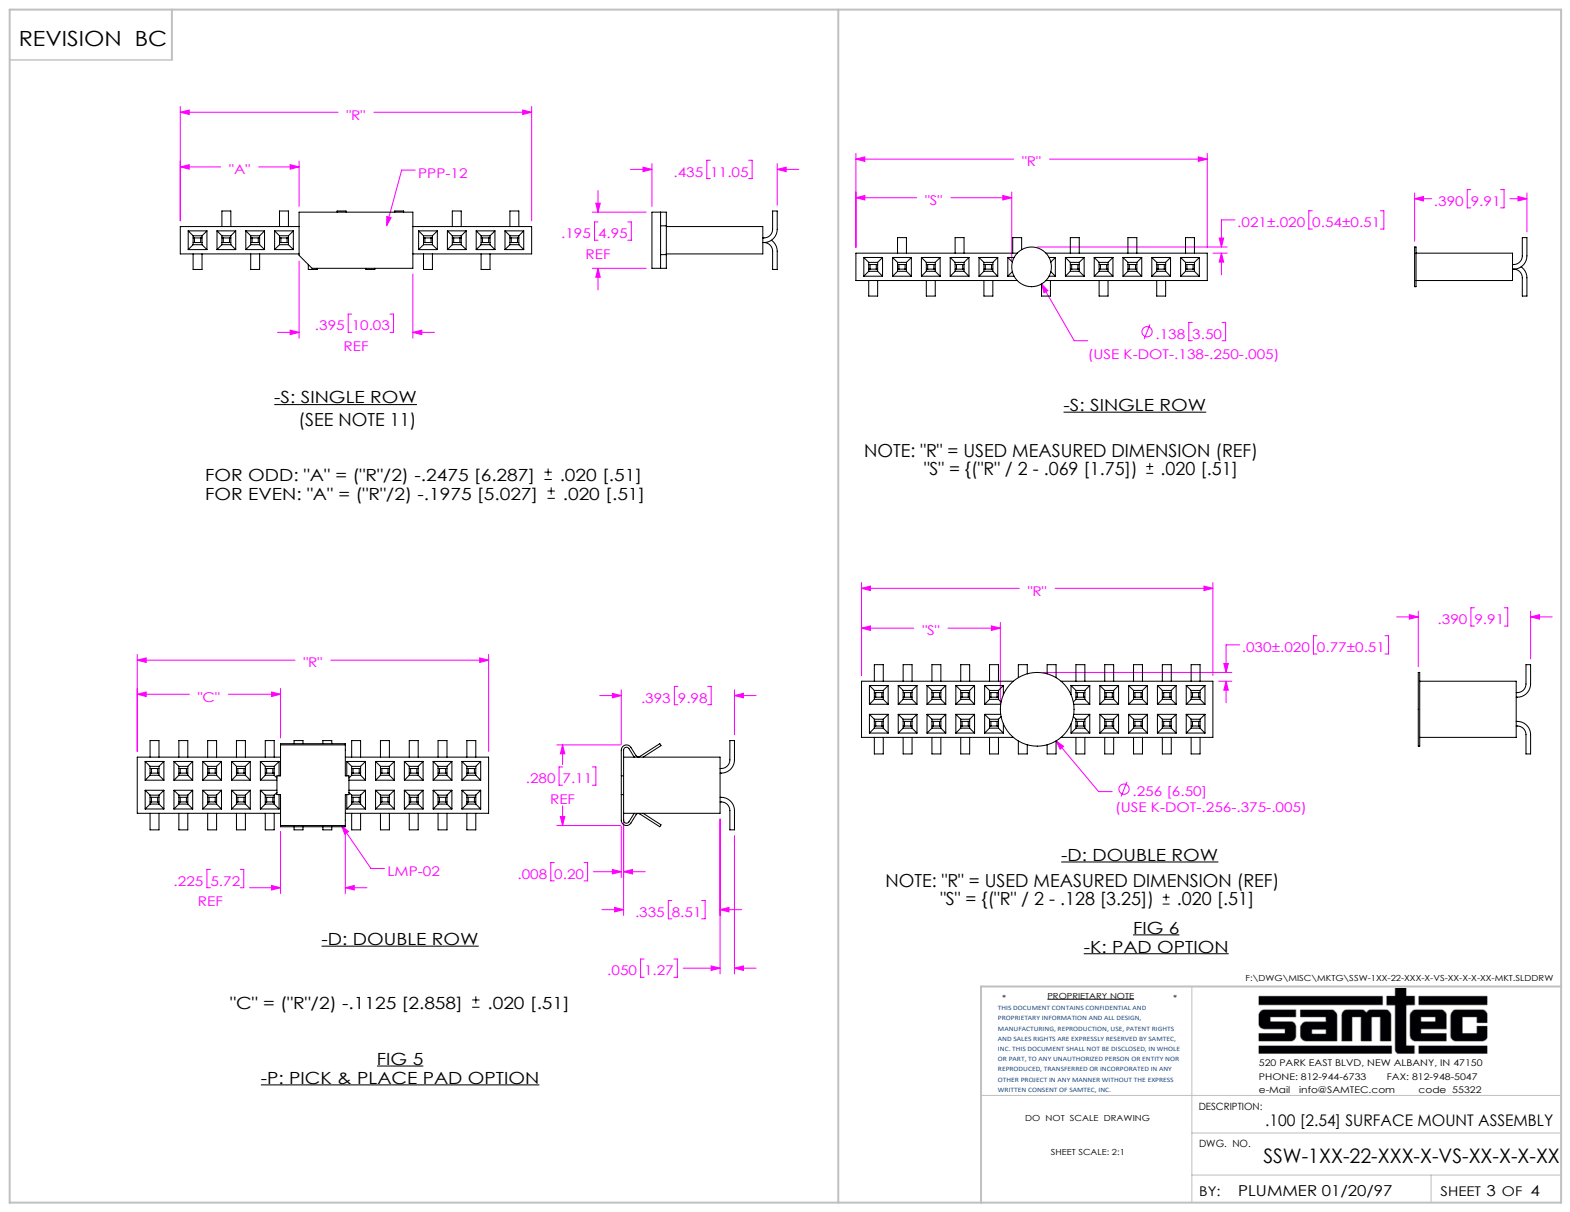
[picture p32: page 3]
-S: SINGLE ROW (SEE NOTE 11); .138 3.50 (USE K-DOT-.138-.250-.005); -S: SINGLE ROW; .256 [6.50] (USE K-DOT-.256-.375-.005); FOR ODD: "A" = ("R"/2) -.2475 [6.287] .020 [.51] FOR EVEN: "A" = ("R"/2) -.1975 [5.027] .020 [.51]; -D: DOUBLE ROW; FIG 5; FIG 6 -K: PAD OPTION; PLUMMER 01/20/97

NOTE: "R" = USED MEASURED DIMENSION (REF)

F:\DWG\MISC\MKTG\SSW-1XX-22-XXX-X-VS-XX-X-X-XX-MKT.SLDDRW

* PROPRIETARY NOTE * THIS DOCUMENT CONTAINS CONFIDENTIAL AND PROPRIETARY INFORMATION AND ALL DESIGN, MANUFACTURING, REPRODUCTION, USE, PATENT RIGHTS AND SALES RIGHTS ARE EXPRESSLY RESERVED BY SAMTEC, INC. THIS DOCUMENT SHALL NOT BE DISCLOSED, IN WHOLE OR PART, TO ANY UNAUTHORIZED PERSON OR ENTITY NOR REPRODUCED, TRANSFERRED OR INCORPORATED IN ANY OTHER PROJECT IN ANY MANNER WITHOUT THE EXPRESS WRITTEN CONSENT OF SAMTEC, INC. | 520 PARK EAST BLVD, NEW ALBANY, IN 47150 PHONE: 812-944-6733 FAX: 812-948-5047 e-Mail info@SAMTEC.com code 55322

-P: PICK & PLACE PAD OPTION

DESCRIPTION: .100 [2.54] SURFACE MOUNT ASSEMBLY

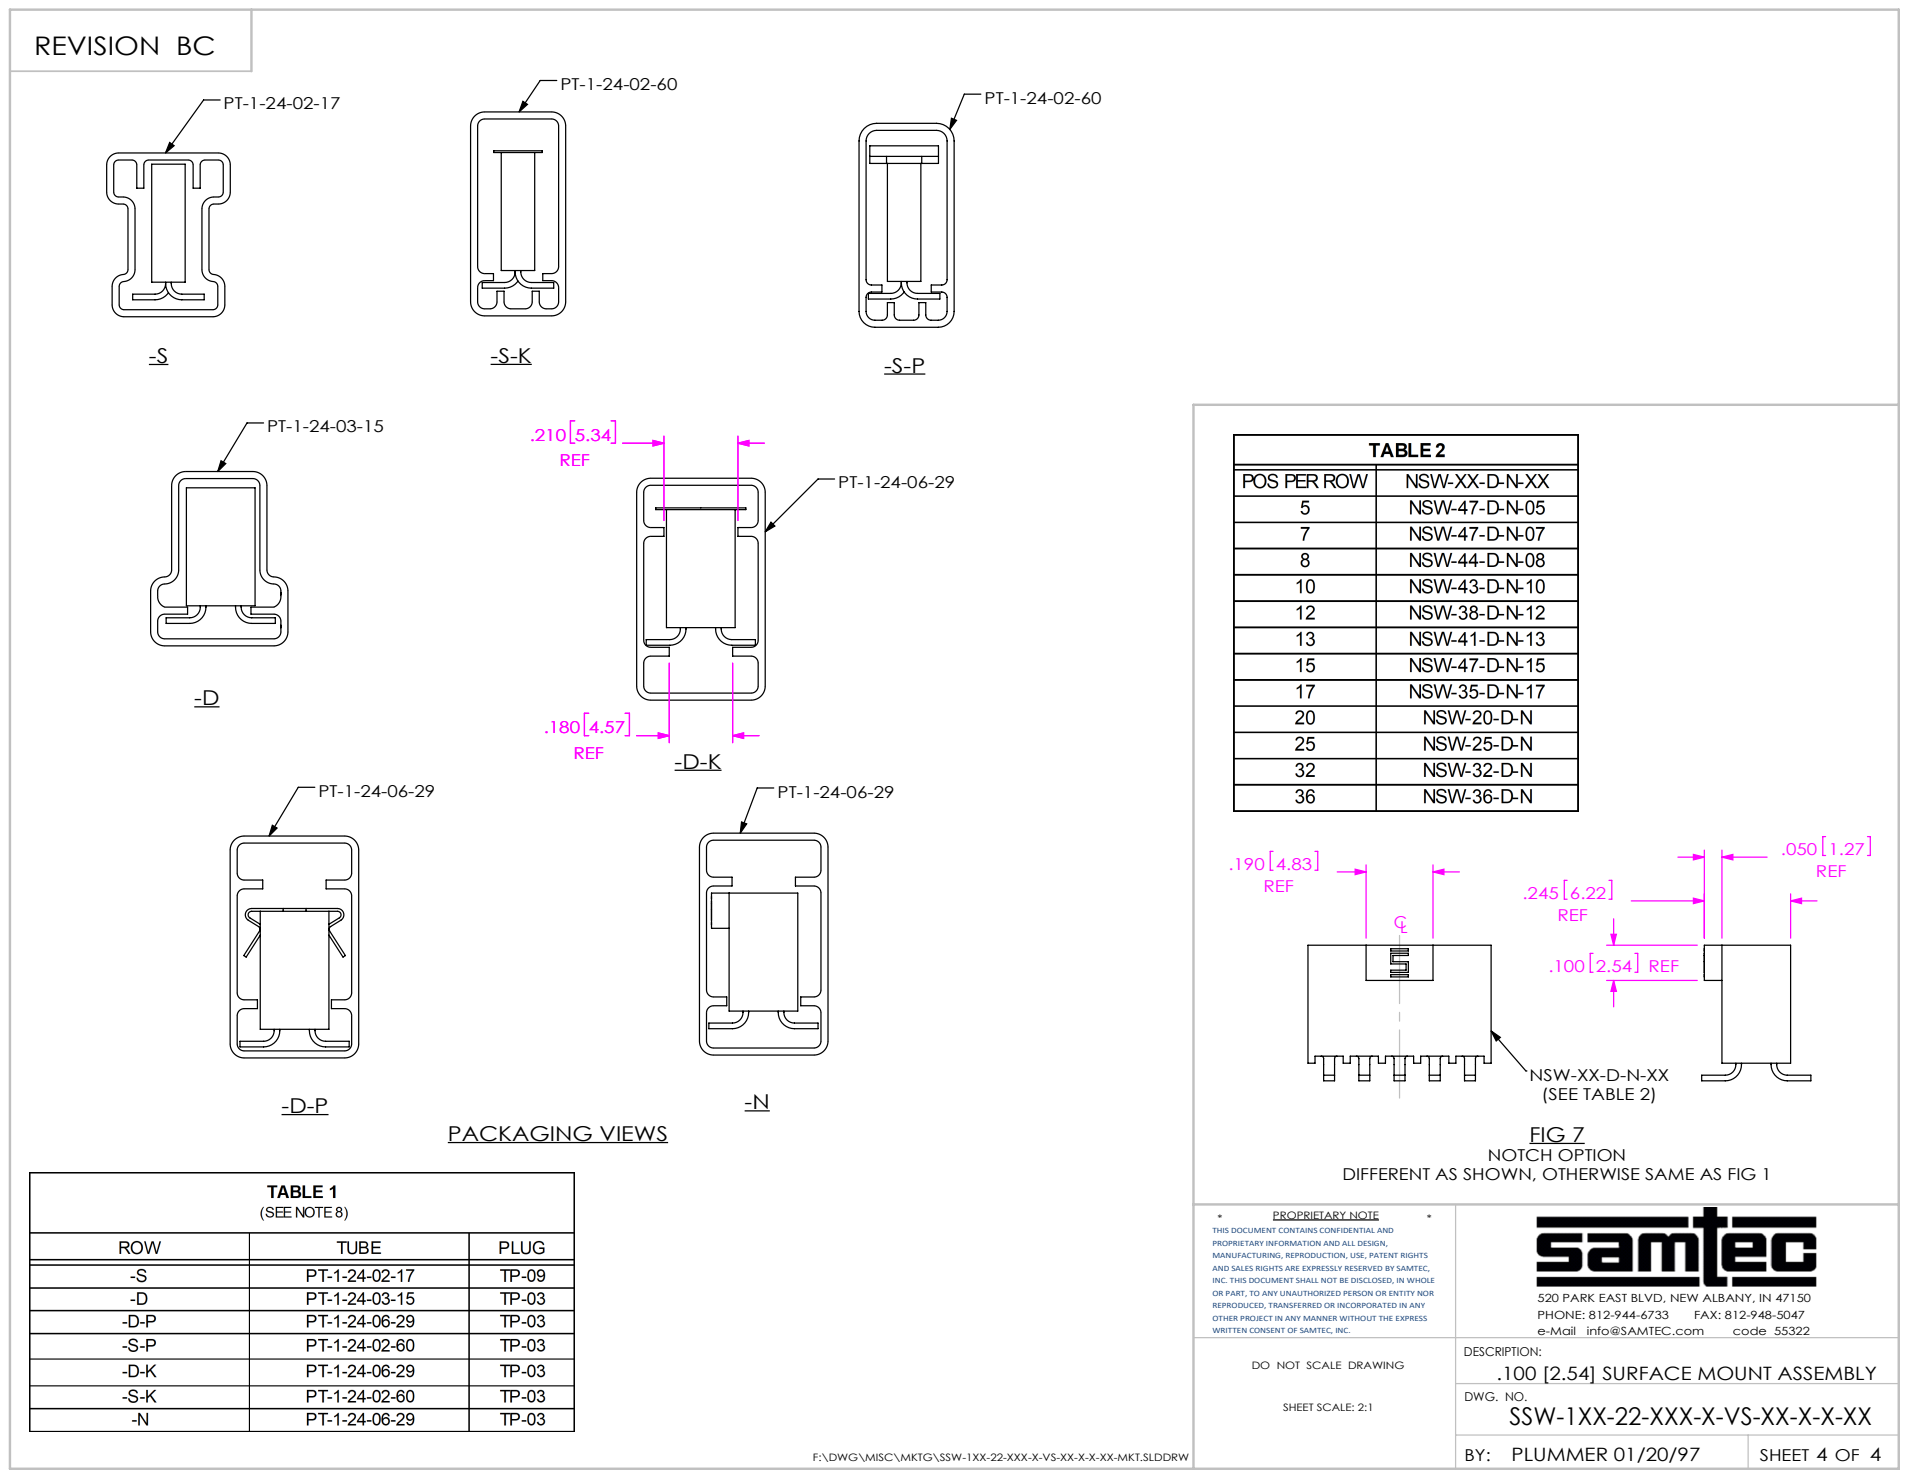
[picture p33: page 4]
PACKAGING VIEWS; PLUMMER 01/20/97

NSW-XX-D-N-XX
(SEE TABLE 2)
FIG 7
NOTCH OPTION

DIFFERENT AS SHOWN, OTHERWISE SAME AS FIG 1

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

DESCRIPTION:
