prakashlab/octopi-driver-board/Parts/ICs/Digital Buffers/NC7SZ125/README.md

# ON Semiconductor NC7SZ125

Documentation and specifications for ON Semiconductor NC7SZ125 tri-state buffers

## License

The PDF files in this directory are copyright ON Semiconductor.
