prakashlab/octopi-driver-board/Parts/ICs/Analog Muxes/74HC4067/README.md

# Nexperia 74HC4067

Documentation and specifications for Nexperia 74HC4067 analog muxes

## License

The PDF files in this directory are copyright Nexperia.
