prakashlab/octopi-driver-board/Parts/ICs/SPI Peripherals/DACx0508/README.md

# Texas Instruments DACx0508

Documentation and specifications for Texas Instruments DACx0408 digital-to-analog converters

## License

The PDF files in this directory are copyright Texas Instruments.
