prakashlab/octopi-driver-board/Parts/ICs/SPI Peripherals/MAX7317/README.md

# Maxim Integrated MAX7317

Documentation and specifications for Maxim Integrated MAX7317 I/O expanders

## License

The PDF files in this directory are copyright Maxim Integrated.
