prakashlab/octopi-driver-board/Parts/Connectors/FunctionMAX FX20/FX20-120S-0.5SV Drawing.pdf

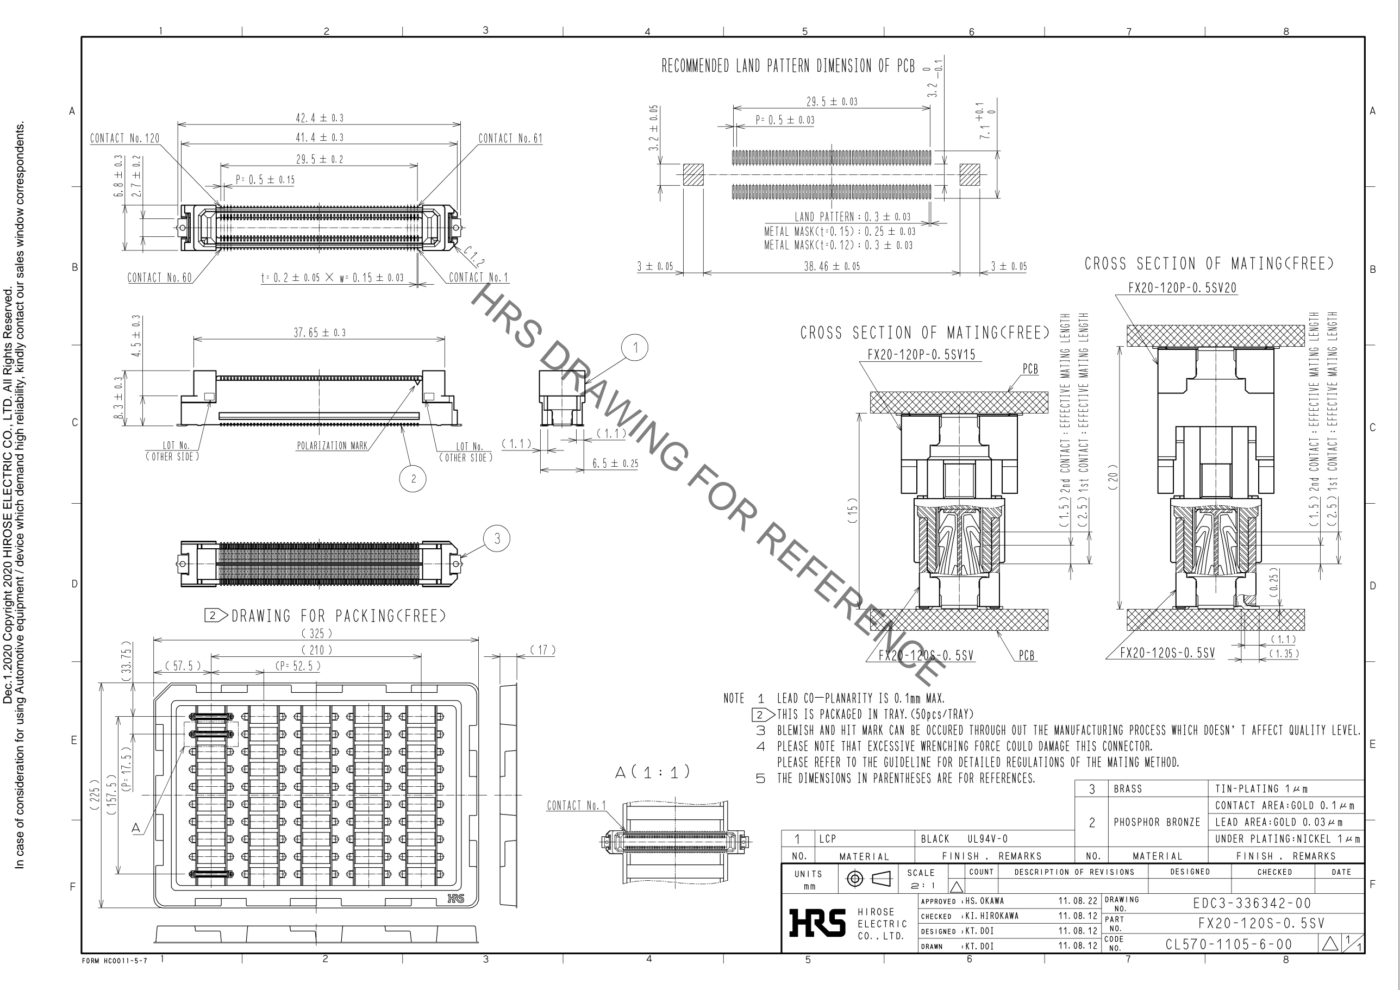
[picture p36: page 1]

HRS DRAWING FOR REFERENCE
