prakashlab/octopi-driver-board/Parts/Fasteners/Keystone Standoffs/24339.step

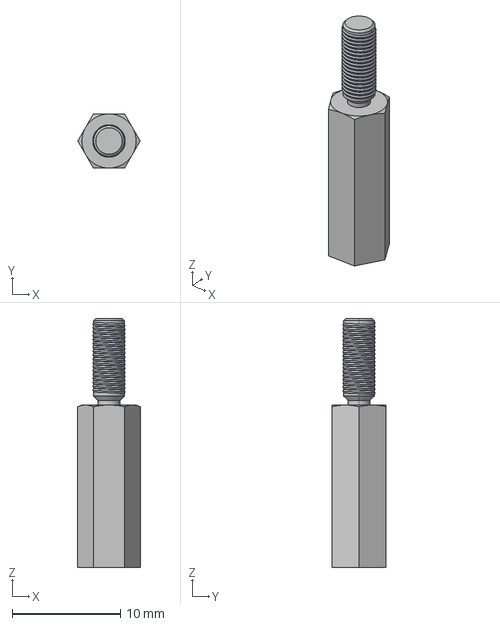
[picture p51: CAD file, 2021-01-23]
Parts/Fasteners/Keystone Standoffs/24339.step
5.77 x 5.00 x 23.0 mm
