prakashlab/octopi-driver-board/Parts/Fasteners/Keystone Standoffs/243xx Drawing.pdf

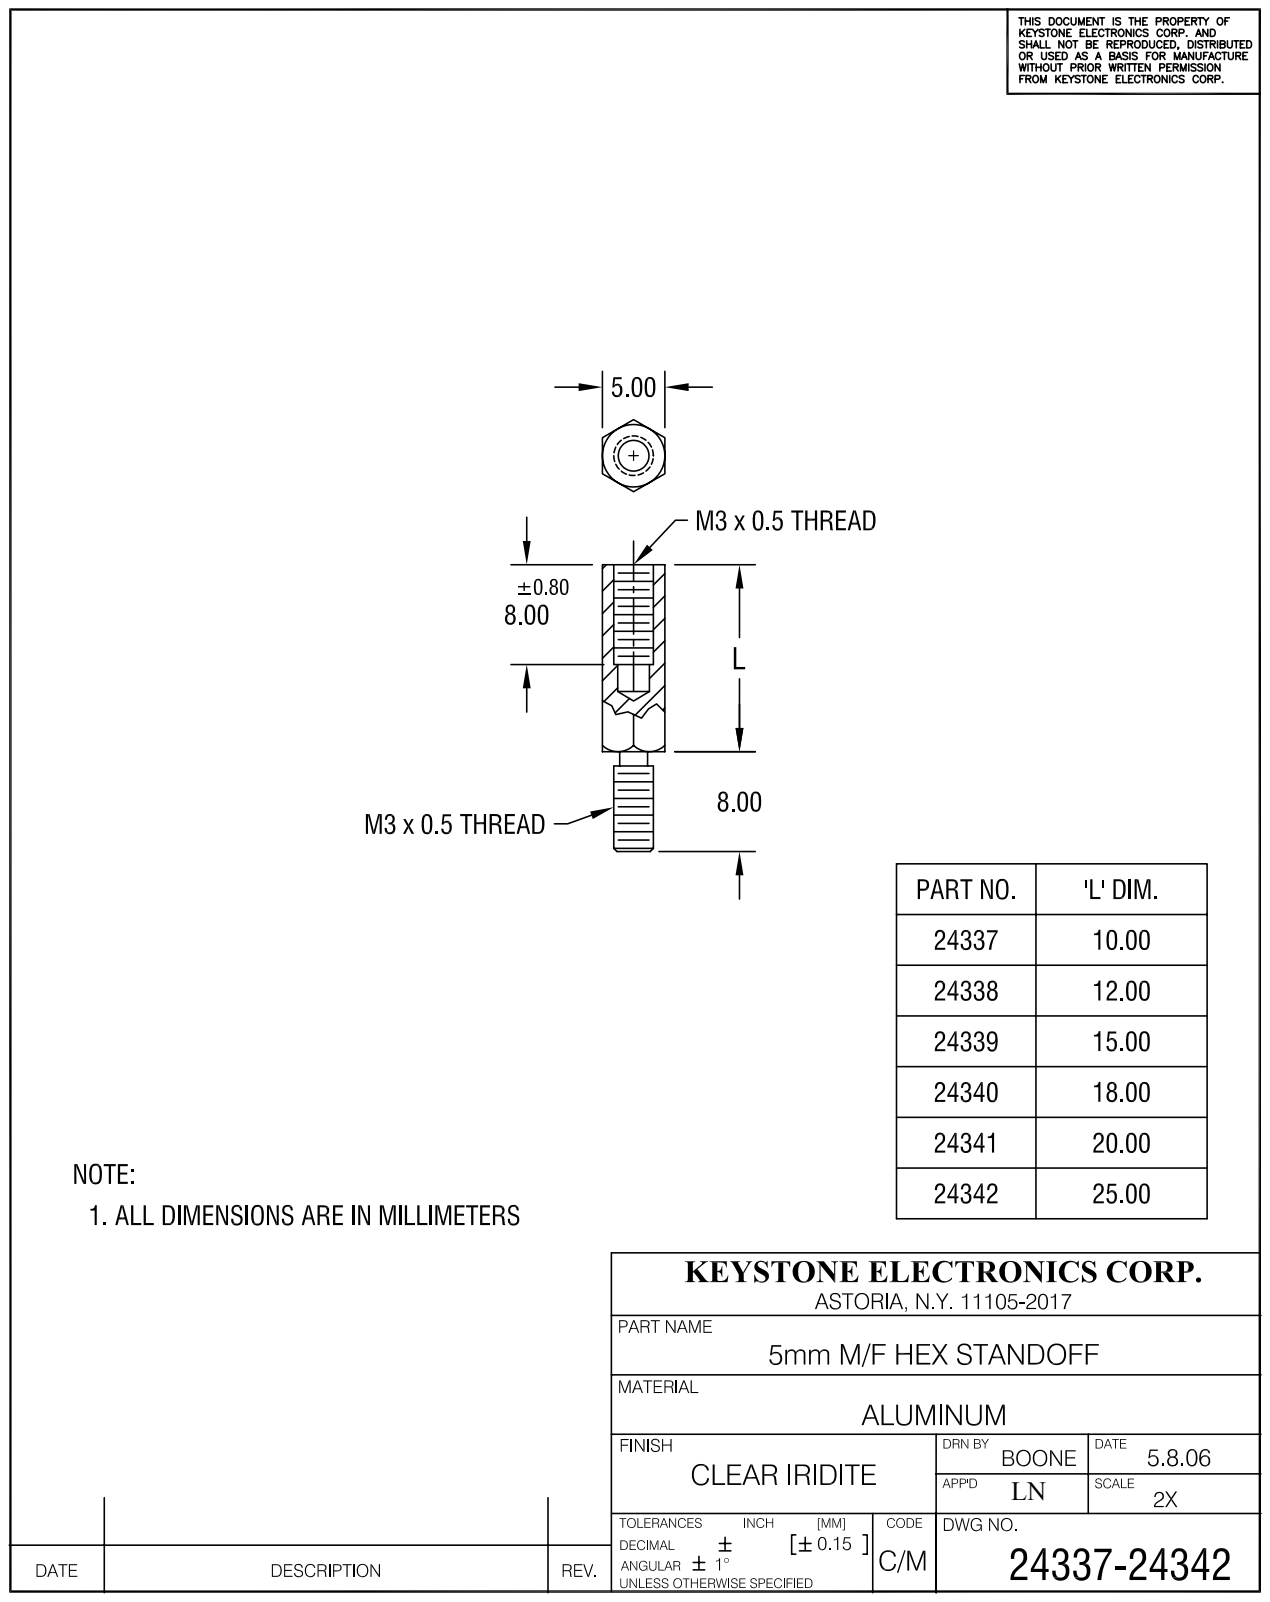
[picture p77: page 1]
