prakashlab/octopi-driver-board/Parts/Fasteners/Keystone Standoffs/244xx Drawing.pdf

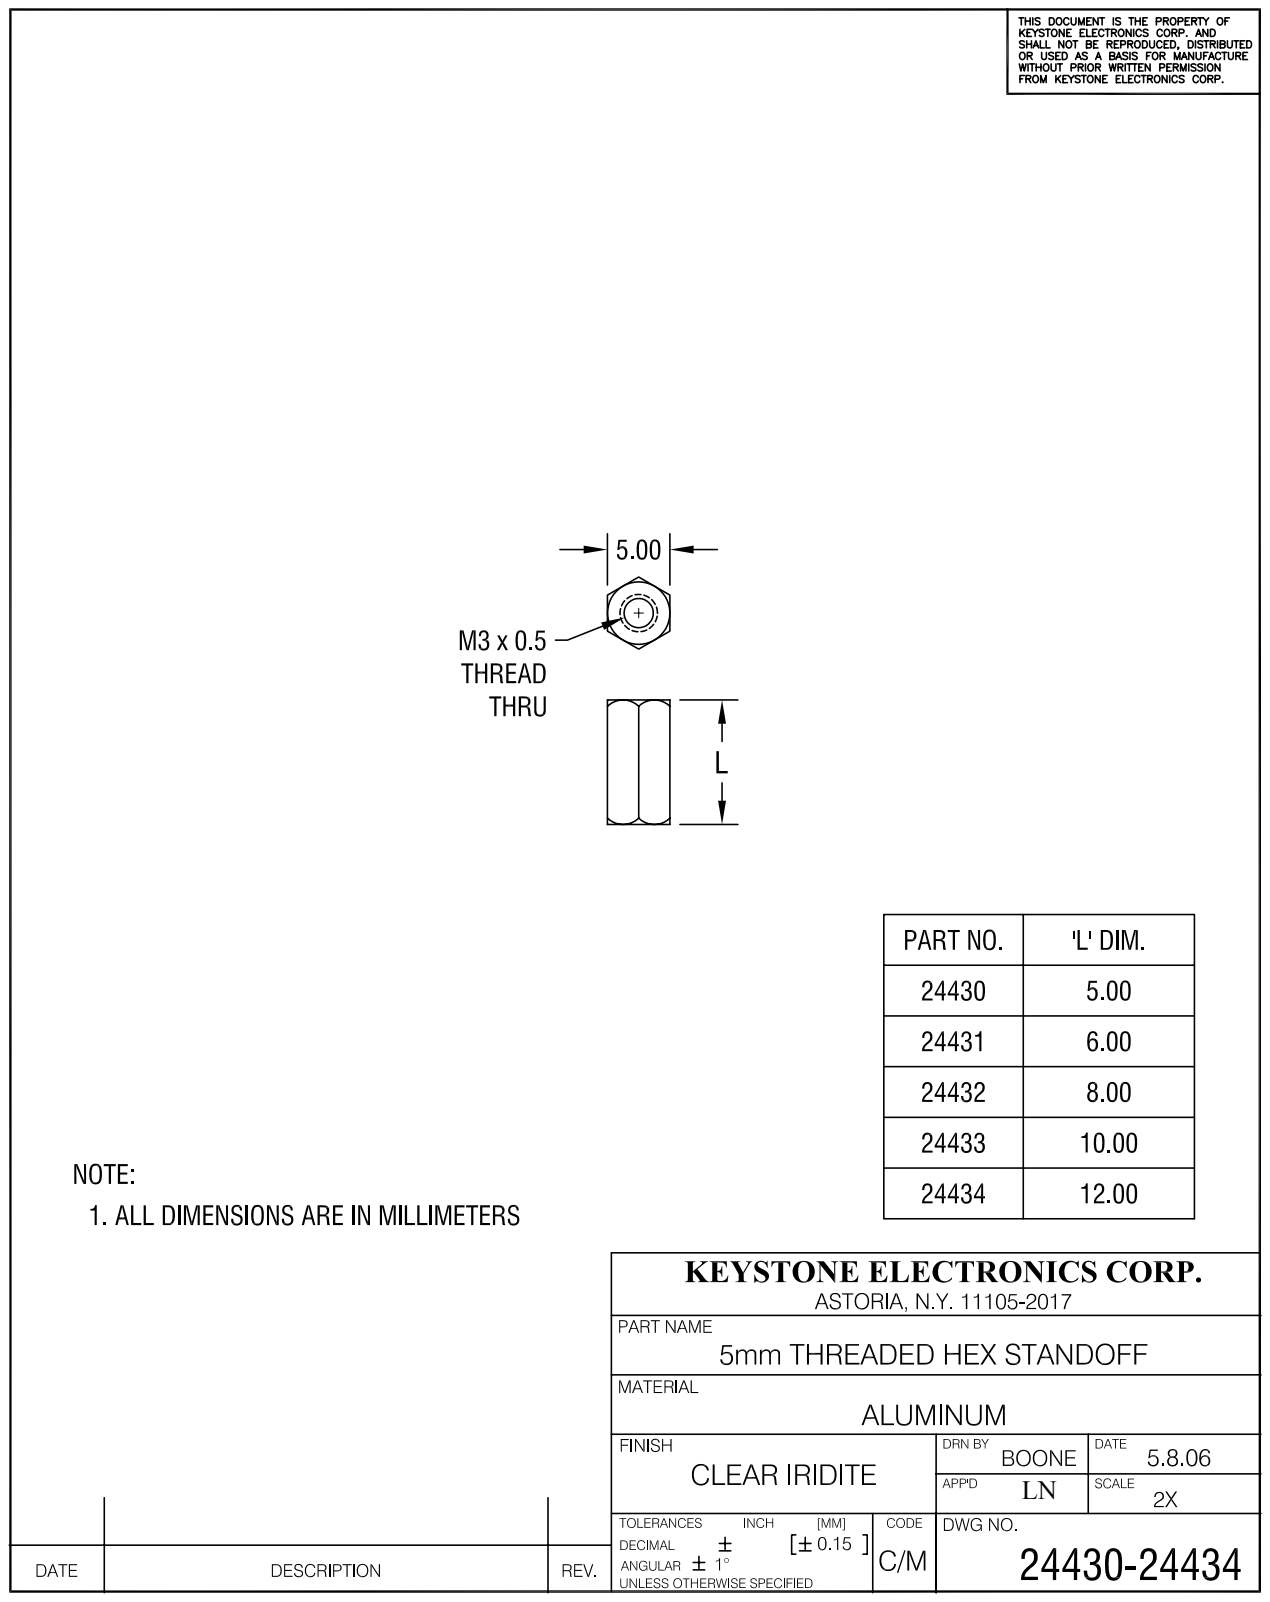
[picture p78: page 1]
